richardjm/Crucible/STLs/panels/clip_3.8/panel_clip_corner_3.8.stl

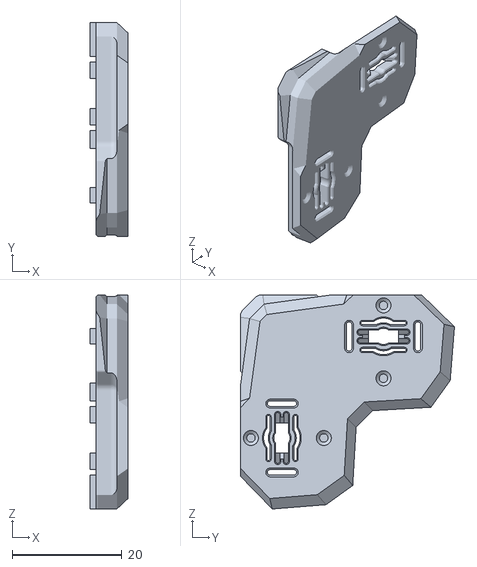
[picture p19: CAD file, 2023-03-05]
STLs/panels/clip_3.8/panel_clip_corner_3.8.stl
6.94 x 38.9 x 38.9
