richardjm/Crucible/STLs/panels/clip_4.8/[t]_panel_key_4.8.stl

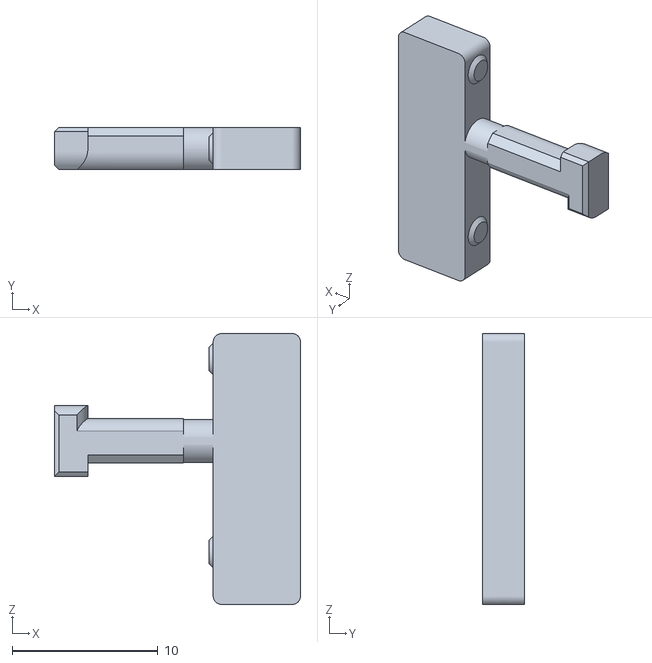
[picture p20: CAD file, 2023-03-05]
STLs/panels/clip_4.8/[t]_panel_key_4.8.stl
16.9 x 2.90 x 18.6
