richardjm/Crucible/STLs/panels/clip_7.0/panel_clip_center_7.0.stl

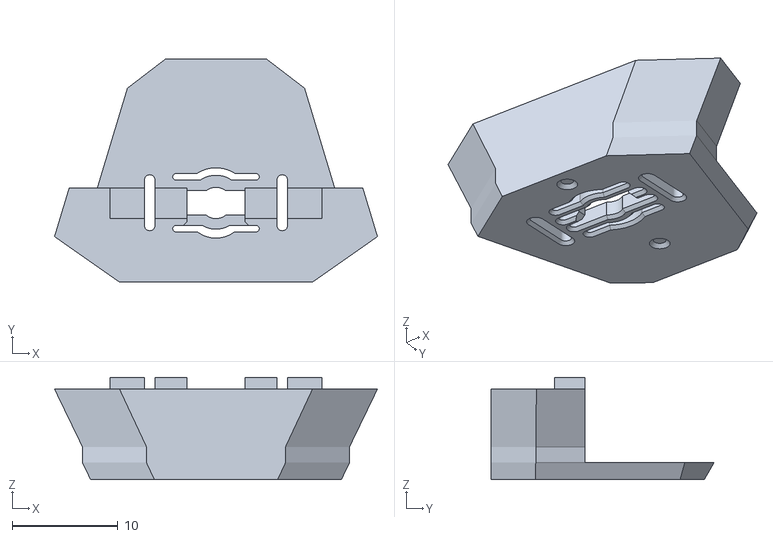
[picture p21: CAD file, 2023-02-03]
STLs/panels/clip_7.0/panel_clip_center_7.0.stl
30.5 x 21.1 x 9.66
