richardjm/Crucible/STLs/spool_holder/[a]_filament_guide_6mm.stl

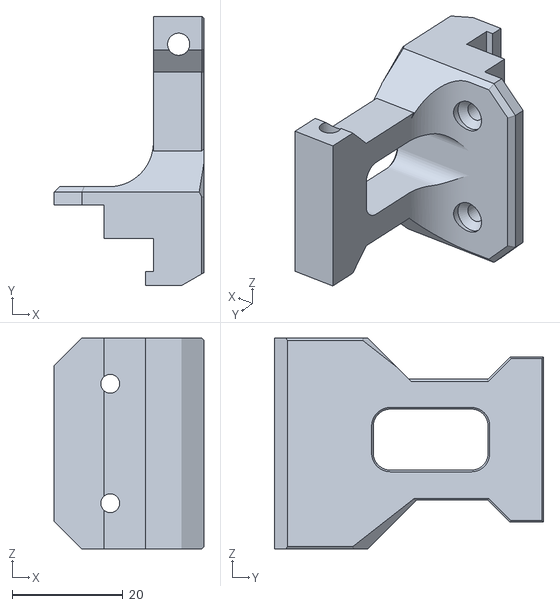
[picture p22: CAD file, 2023-04-07]
STLs/spool_holder/[a]_filament_guide_6mm.stl
27.0 x 48.5 x 38.0
