richardjm/Crucible/STLs/spoolholder.stl

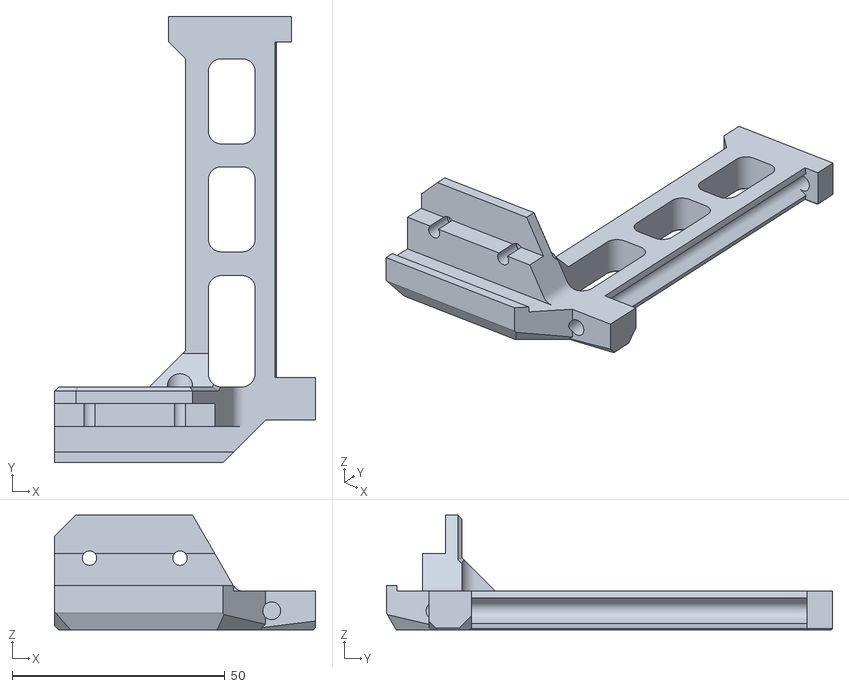
[picture p23: CAD file, 2023-01-31]
STLs/spoolholder.stl
61.4 x 105.0 x 27.0
