richardjm/Crucible/STLs/stealth_skirts/4010_Side_Skirt_Mid_Solid_x2.stl

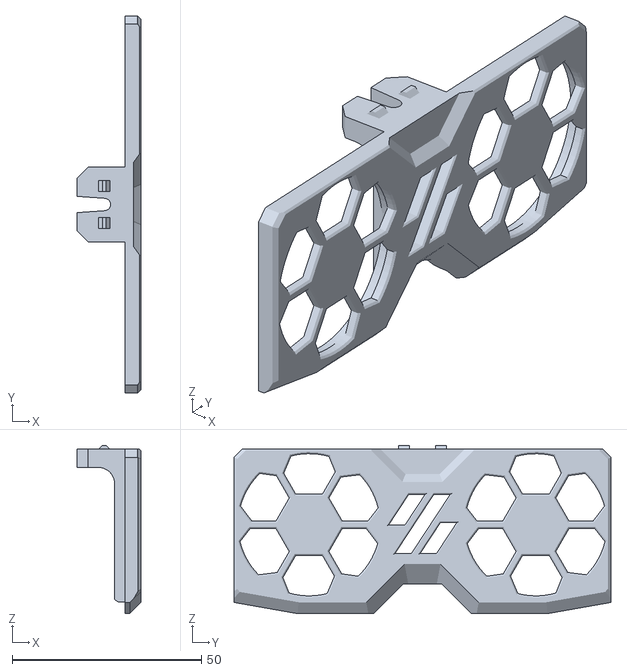
[picture p24: CAD file, 2023-04-01]
STLs/stealth_skirts/4010_Side_Skirt_Mid_Solid_x2.stl
17.0 x 99.7 x 44.5
