richardjm/Crucible/STLs/tools/MGN9_Rail_Guide_x2.stl

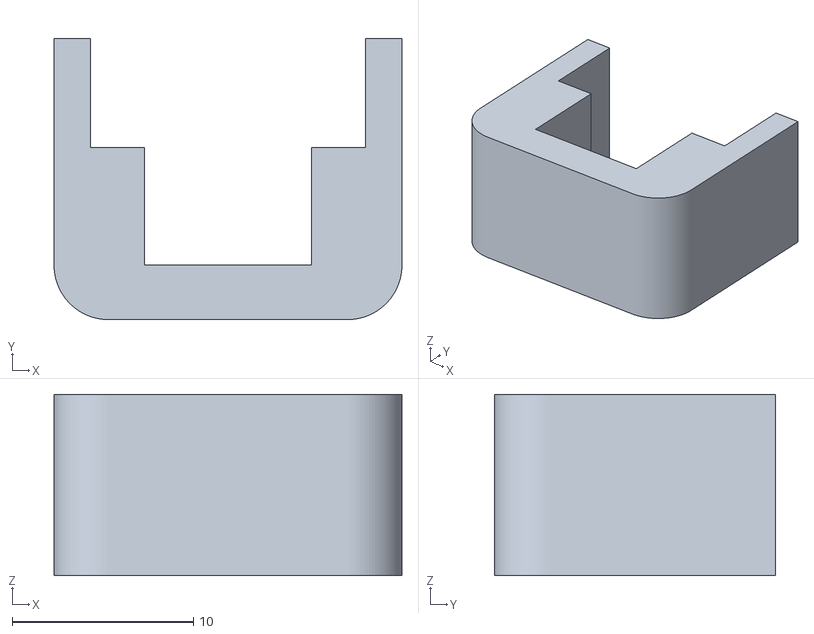
[picture p25: CAD file, 2023-02-28]
STLs/tools/MGN9_Rail_Guide_x2.stl
19.2 x 15.5 x 10.0
