richardjm/Crucible/Usermods/richardjm/carriage-slimmed/[a]_x_carriage-5.95.stl

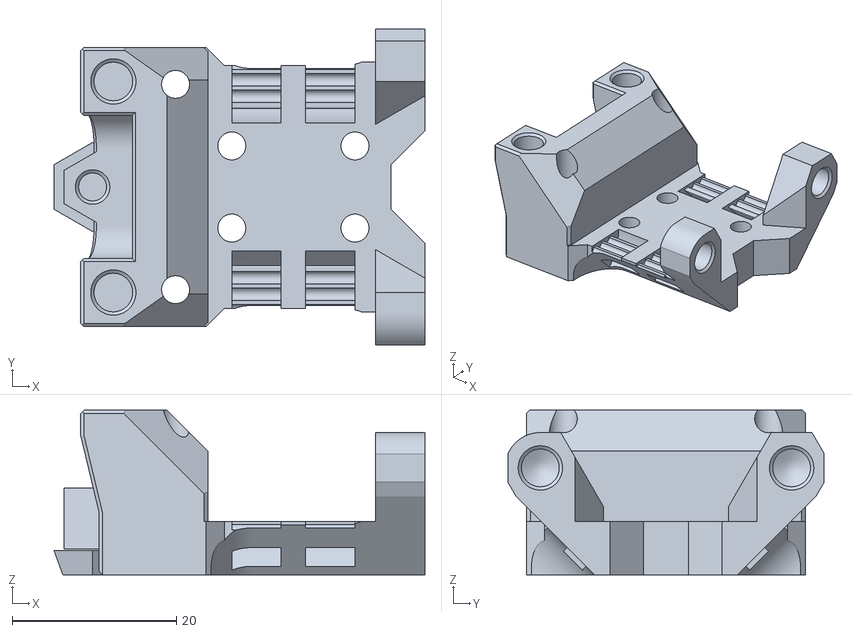
[picture p26: CAD file, 2023-02-17]
Usermods/richardjm/carriage-slimmed/[a]_x_carriage-5.95.stl
45.2 x 38.5 x 20.1
