richardjm/Crucible/Usermods/richardjm/extrusionless-x/boop/magnet_carrier_right.stl

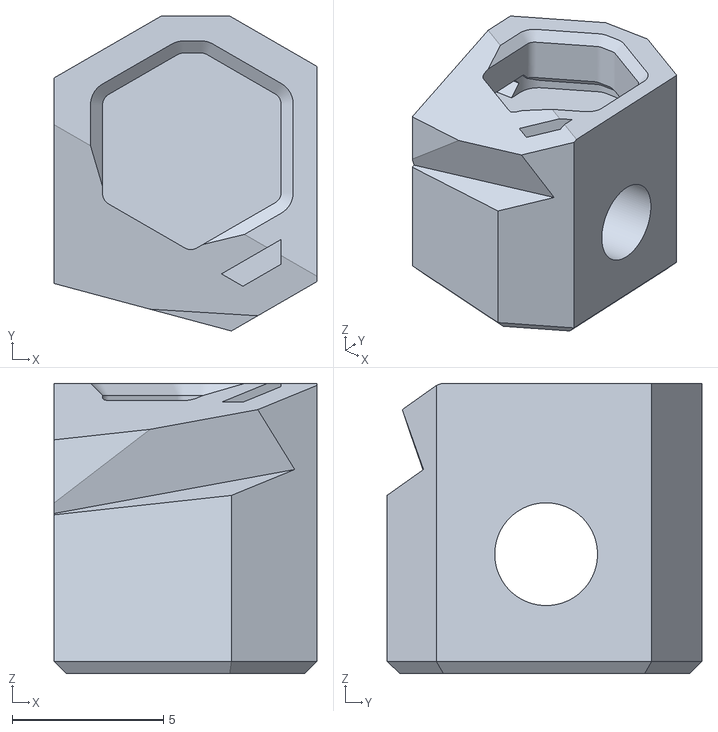
[picture p28: CAD file, 2025-10-05]
Usermods/richardjm/extrusionless-x/boop/magnet_carrier_right.stl
8.70 x 10.4 x 9.60
