richardjm/Crucible/Usermods/richardjm/flysht36-mount/FlySht36v2Mount.stl

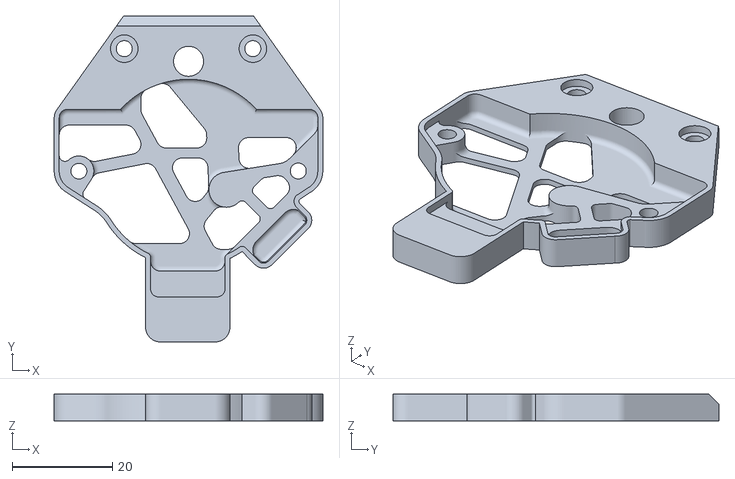
[picture p30: CAD file, 2023-02-16]
Usermods/richardjm/flysht36-mount/FlySht36v2Mount.stl
53.7 x 65.1 x 5.33
