richardjm/Crucible/Usermods/richardjm/frond-bed-cover/FrontBedCover-15mmBrassSpacer.stl

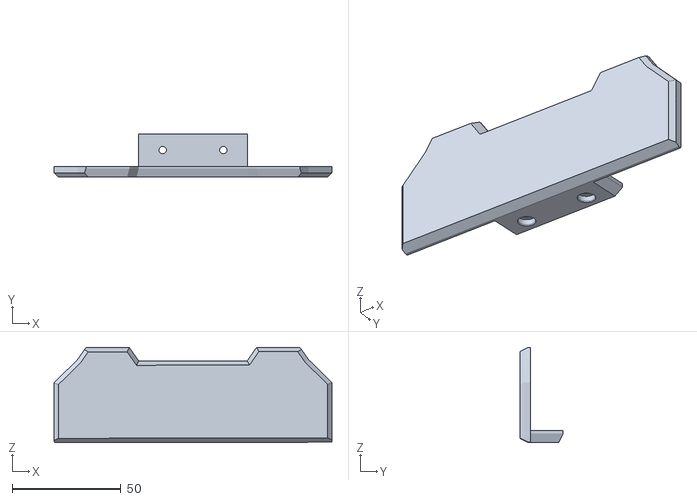
[picture p31: CAD file, 2023-03-17]
Usermods/richardjm/frond-bed-cover/FrontBedCover-15mmBrassSpacer.stl
128.1 x 20.0 x 43.9
