richardjm/Crucible/Usermods/richardjm/idle_idea/IdleIdea2 v13 - CarrierA.stl

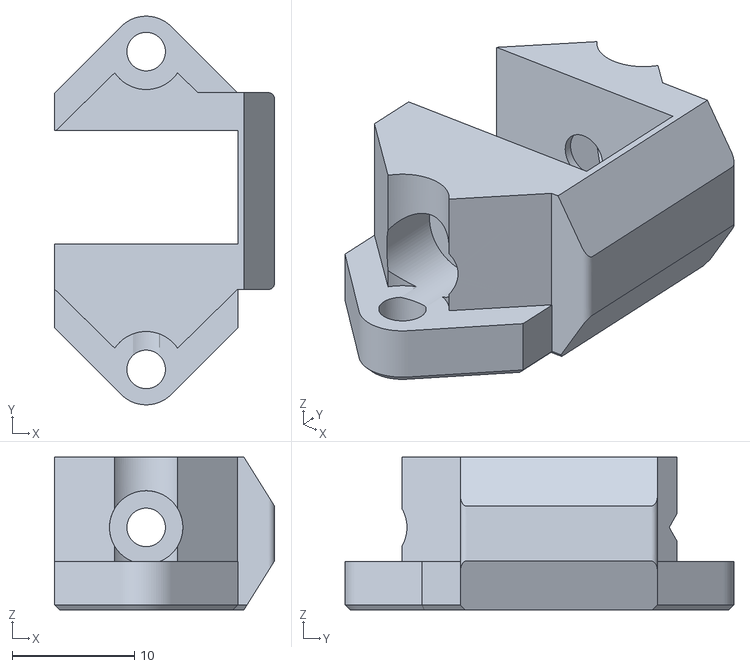
[picture p32: CAD file, 2023-04-13]
Usermods/richardjm/idle_idea/IdleIdea2 v13 - CarrierA.stl
18.0 x 31.8 x 12.5
