richardjm/Crucible/Usermods/richardjm/idler_beefy/idler_b_arm.stl

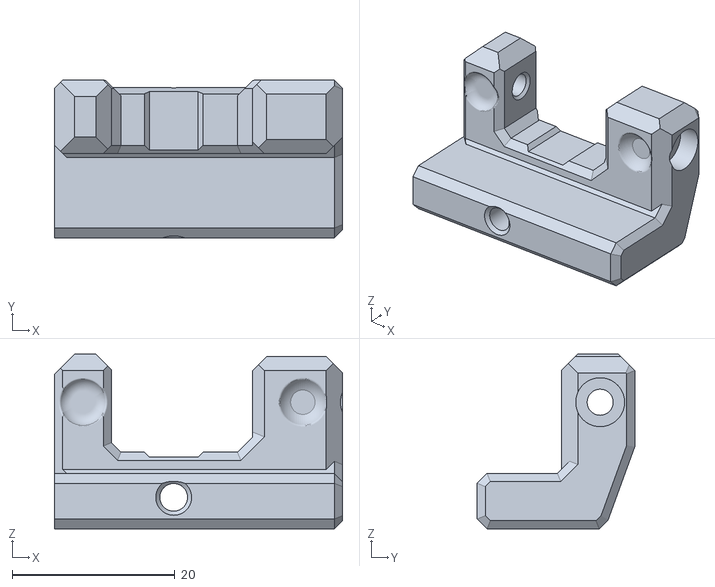
[picture p33: CAD file, 2023-04-13]
Usermods/richardjm/idler_beefy/idler_b_arm.stl
35.4 x 19.4 x 21.4
