richardjm/Crucible/Usermods/richardjm/leds/crucible_led_sawtooth_100mm.stl

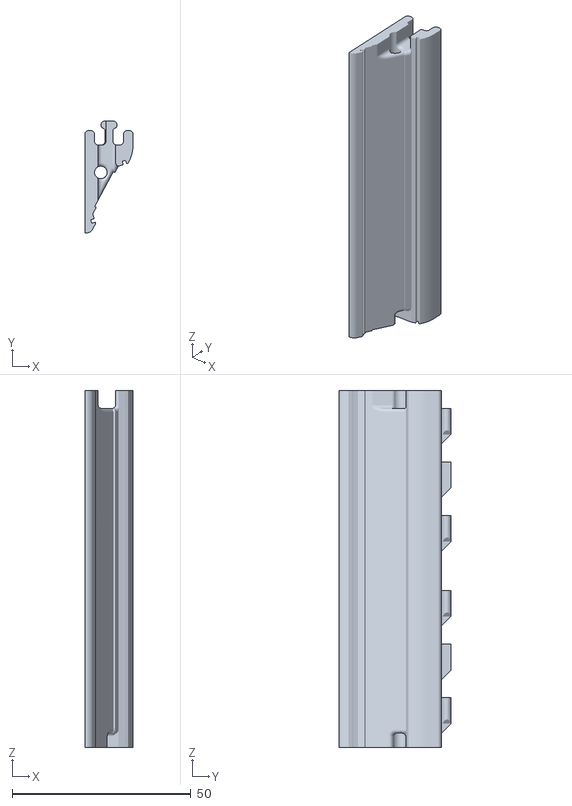
[picture p34: CAD file, 2023-02-11]
Usermods/richardjm/leds/crucible_led_sawtooth_100mm.stl
13.5 x 31.4 x 100.0
