richardjm/Crucible/Usermods/richardjm/pointy-stop/rail-stop.stl

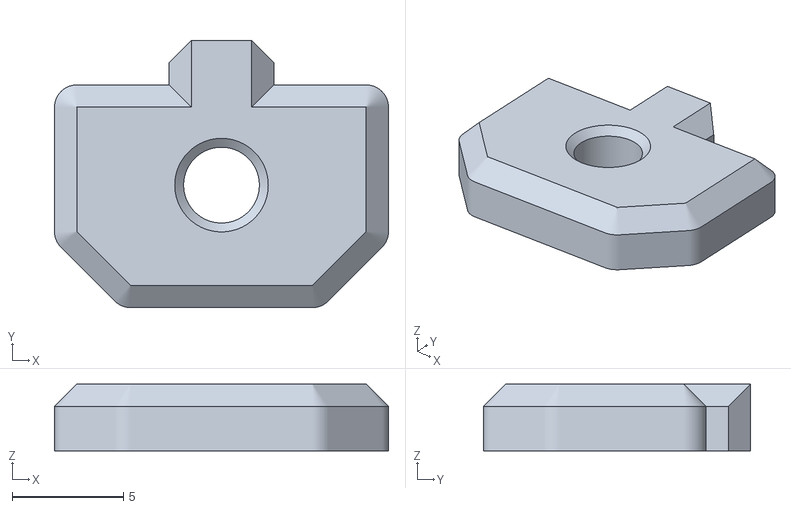
[picture p35: CAD file, 2023-02-24]
Usermods/richardjm/pointy-stop/rail-stop.stl
15.0 x 12.0 x 3.00
