richardjm/Crucible/Usermods/richardjm/puppet-pi-mount/PuppetPi.stl

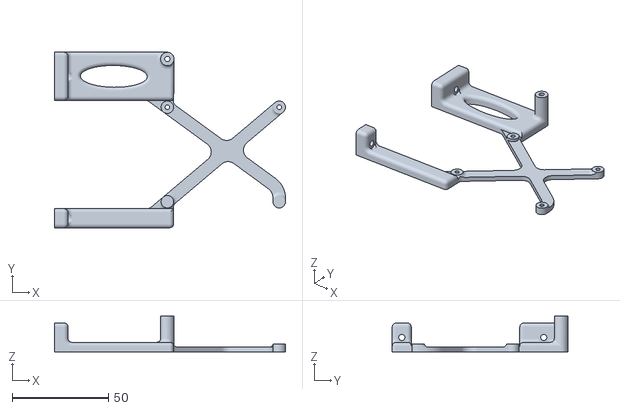
[picture p36: CAD file, 2023-03-19]
Usermods/richardjm/puppet-pi-mount/PuppetPi.stl
119.8 x 91.0 x 18.6
