richardjm/Crucible/Usermods/richardjm/short-rear-z/Z_ChainMount_w_cable.stl

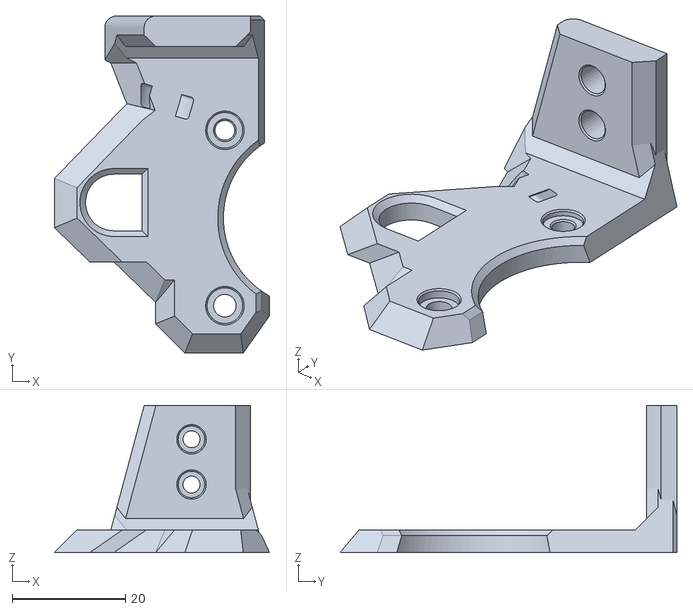
[picture p37: CAD file, 2023-03-19]
Usermods/richardjm/short-rear-z/Z_ChainMount_w_cable.stl
38.0 x 59.6 x 26.0
