richardjm/Crucible/Usermods/richardjm/UnKlickyNG/STL/ProbeMount_Body3_Wedge.stl

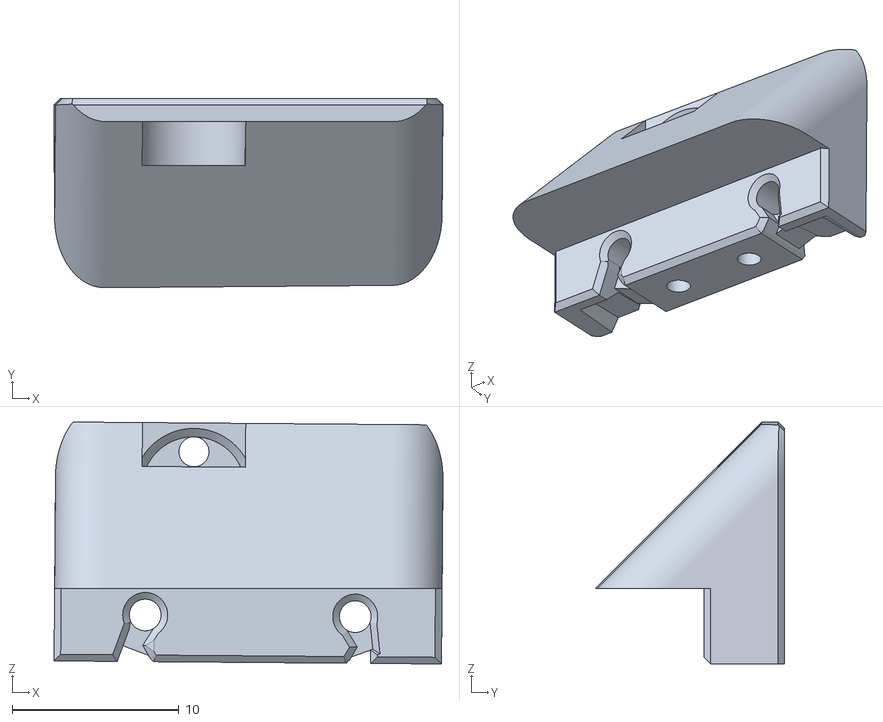
[picture p38: CAD file, 2023-03-13]
Usermods/richardjm/UnKlickyNG/STL/ProbeMount_Body3_Wedge.stl
23.3 x 11.4 x 14.5
