richardjm/Crucible/STLs/frame/[a]_rail_stop_x6.stl

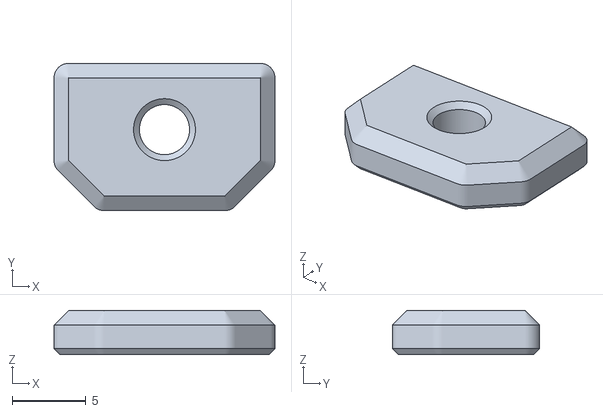
[picture p39: CAD file, 2023-02-13]
STLs/frame/[a]_rail_stop_x6.stl
15.0 x 10.0 x 3.00
