richardjm/Crucible/STLs/gantry/a_drive_lower_no_fittings.stl

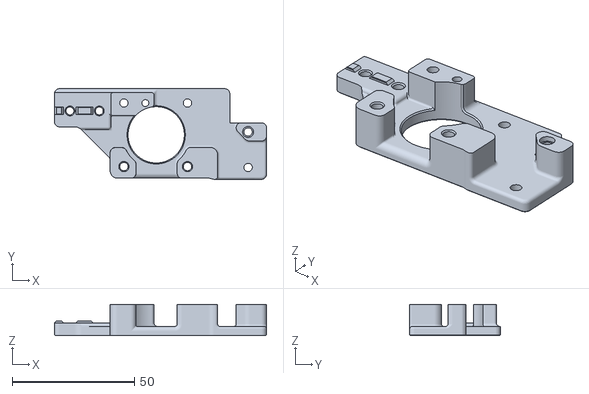
[picture p40: CAD file, 2023-02-12]
STLs/gantry/a_drive_lower_no_fittings.stl
86.7 x 37.0 x 12.8
