richardjm/Crucible/STLs/handles/[t]_handle_part2_x2.stl.stl

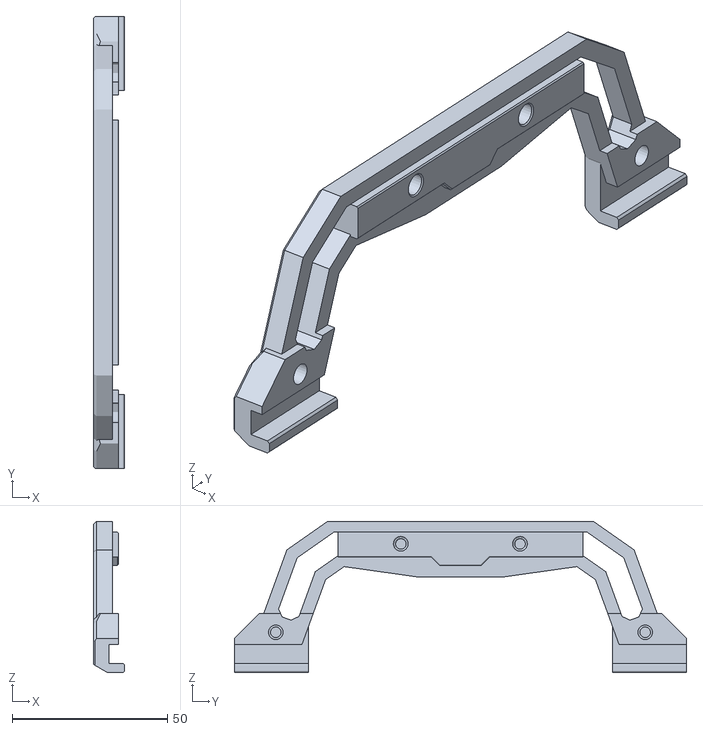
[picture p41: CAD file, 2023-04-07]
STLs/handles/[t]_handle_part2_x2.stl.stl
10.0 x 145.7 x 48.8
