richardjm/Crucible/STLs/klicky/probe.stl

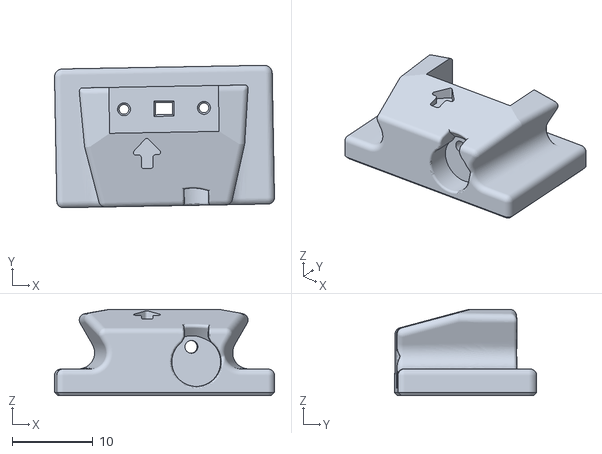
[picture p42: CAD file, 2023-02-26]
STLs/klicky/probe.stl
27.3 x 17.7 x 10.7
