richardjm/Crucible/STLs/mini_stealthburner/[a]_front_cowling.stl

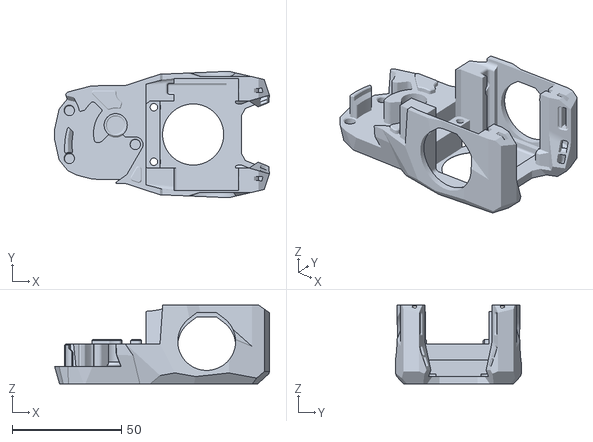
[picture p43: CAD file, 2023-02-13]
STLs/mini_stealthburner/[a]_front_cowling.stl
98.6 x 57.9 x 36.1
