richardjm/Crucible/STLs/mini_stealthburner/hotends/[a]_Hotend_Mount_Revo_Voron.stl

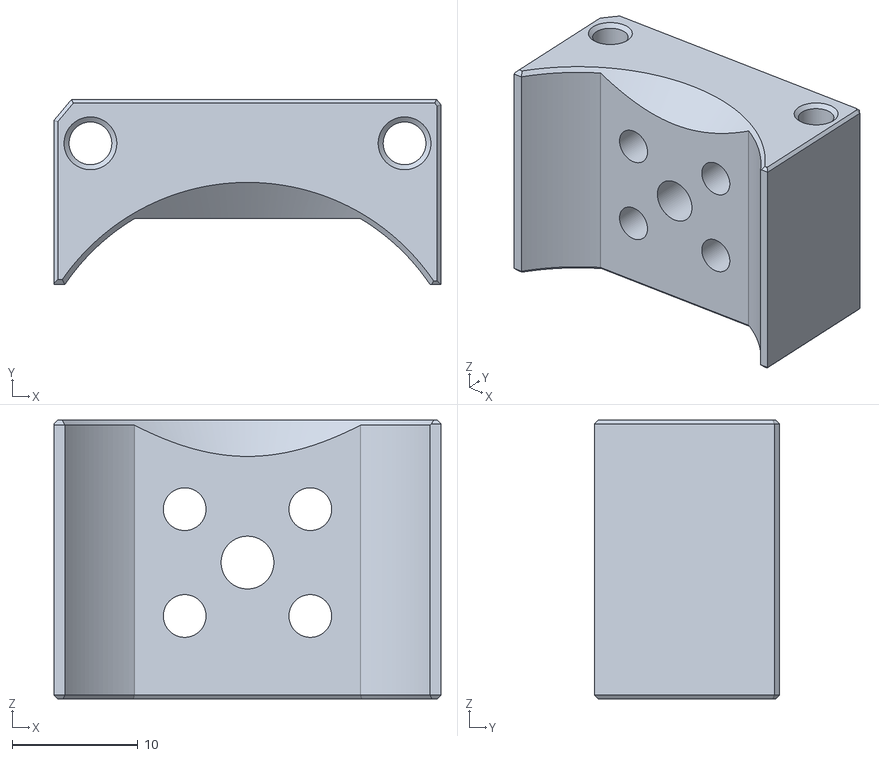
[picture p44: CAD file, 2023-02-12]
STLs/mini_stealthburner/hotends/[a]_Hotend_Mount_Revo_Voron.stl
30.8 x 14.7 x 22.2
