richardjm/Crucible/STLs/panels/clip_2.8/panel_clip_center_2.8.stl

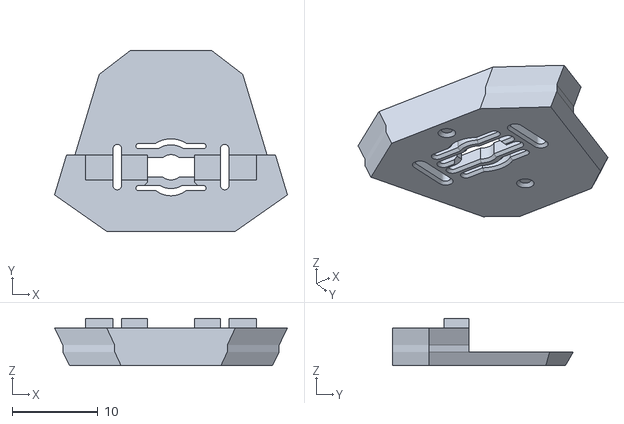
[picture p45: CAD file, 2023-02-04]
STLs/panels/clip_2.8/panel_clip_center_2.8.stl
27.2 x 21.1 x 5.50
