richardjm/Crucible/STLs/panels/clip_3.8/panel_clip_center_3.8.stl

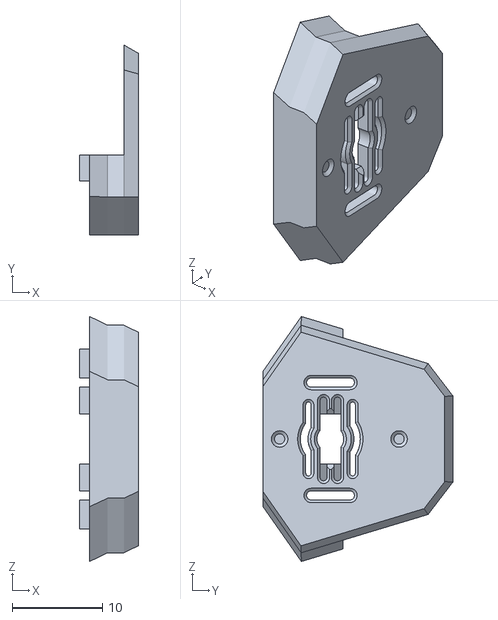
[picture p46: CAD file, 2023-03-05]
STLs/panels/clip_3.8/panel_clip_center_3.8.stl
6.50 x 21.1 x 27.2
