richardjm/Crucible/STLs/panels/clip_4.8/panel_clip_corner_4.8.stl

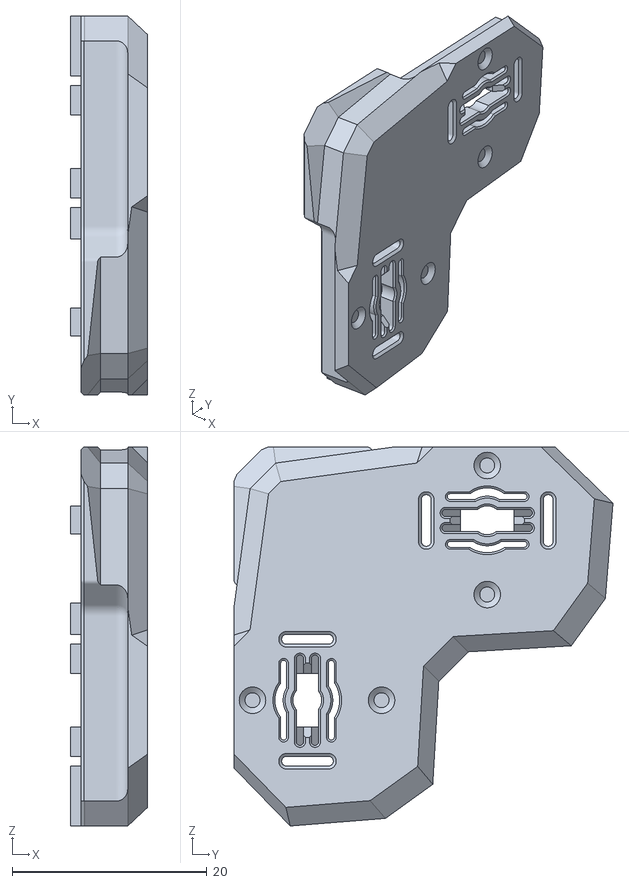
[picture p47: CAD file, 2023-03-05]
STLs/panels/clip_4.8/panel_clip_corner_4.8.stl
7.94 x 38.9 x 38.9
