richardjm/Crucible/STLs/panels/clip_7.0/panel_clip_corner_7.0.stl

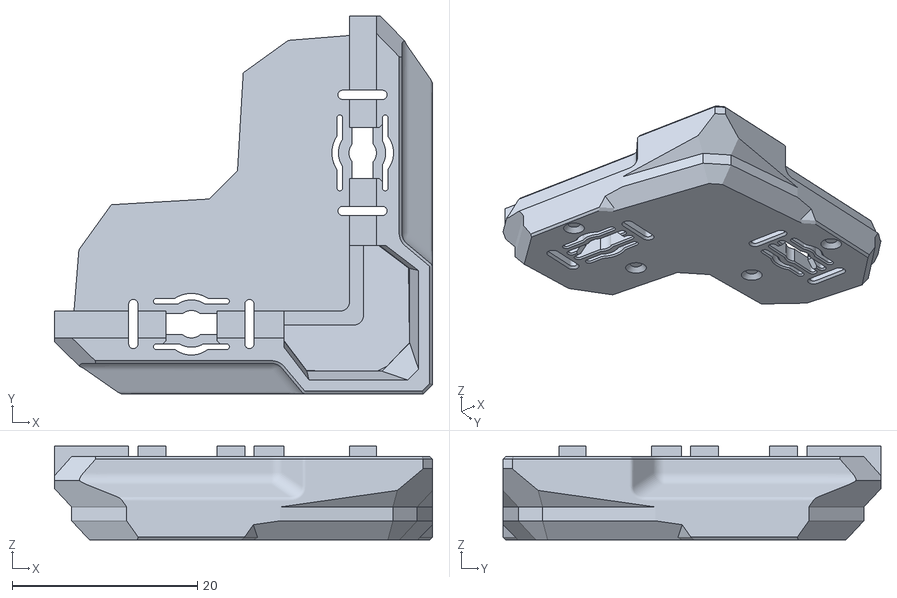
[picture p48: CAD file, 2023-02-03]
STLs/panels/clip_7.0/panel_clip_corner_7.0.stl
40.8 x 40.8 x 10.1
