richardjm/Crucible/STLs/panels/door_hinge_m3x40_x2.stl

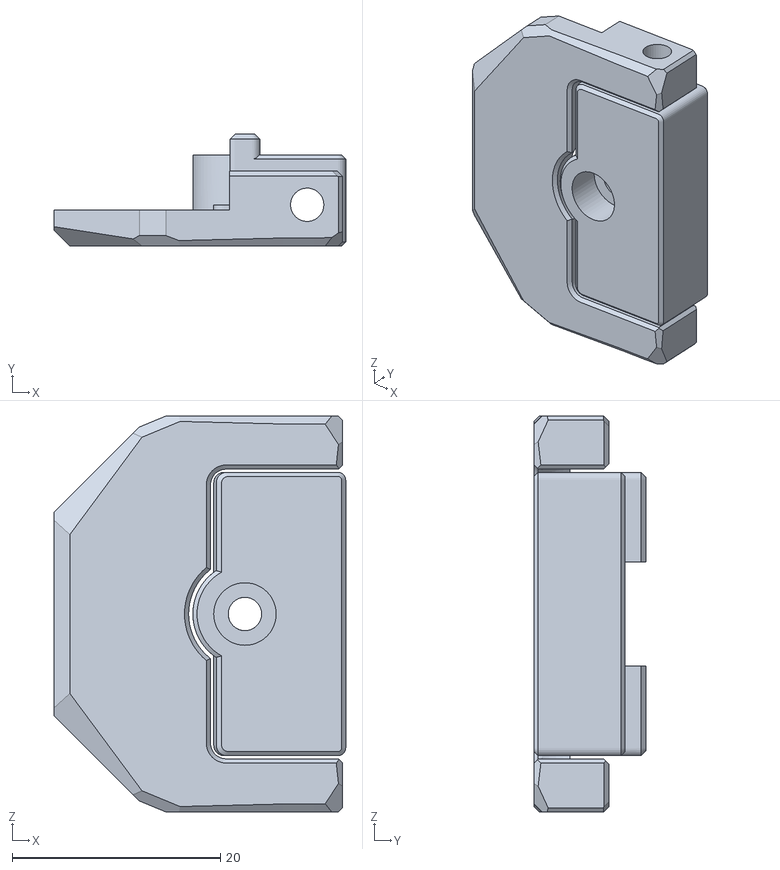
[picture p49: CAD file, 2023-04-02]
STLs/panels/door_hinge_m3x40_x2.stl
28.0 x 10.8 x 38.0
