richardjm/Crucible/STLs/spool_holder/[a]_spool_holder_6mm.stl

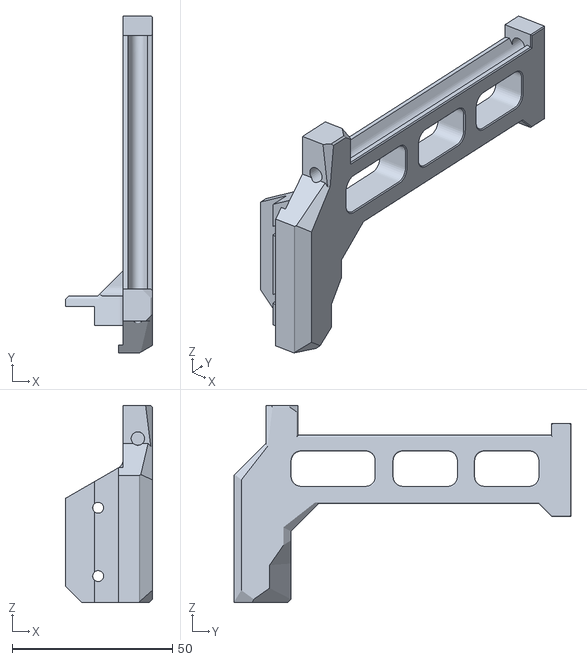
[picture p50: CAD file, 2023-04-07]
STLs/spool_holder/[a]_spool_holder_6mm.stl
27.0 x 105.0 x 61.4
