richardjm/Crucible/STLs/stealth_skirts/Rear_Skirt_Crucible_x1.stl

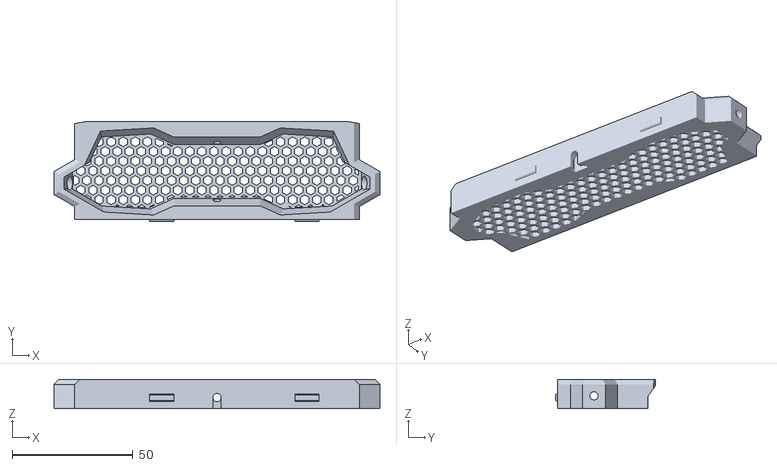
[picture p51: CAD file, 2023-04-01]
STLs/stealth_skirts/Rear_Skirt_Crucible_x1.stl
134.7 x 41.5 x 12.0
