richardjm/Crucible/STLs/z_assembly/z_rear_lower_circular_tnut.stl

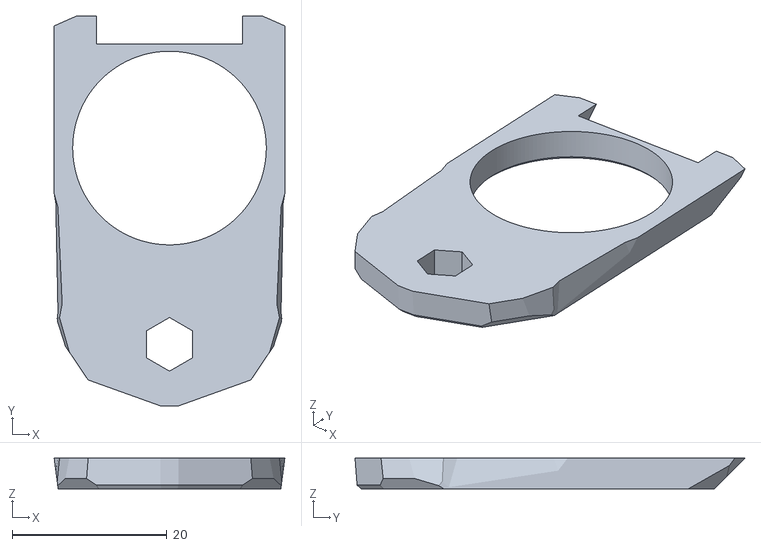
[picture p52: CAD file, 2023-02-11]
STLs/z_assembly/z_rear_lower_circular_tnut.stl
29.8 x 50.4 x 4.00
