richardjm/Crucible/Usermods/richardjm/carriage-slimmed/[a]_strain_relief_spacer_extra_beef-5.95_x2.stl

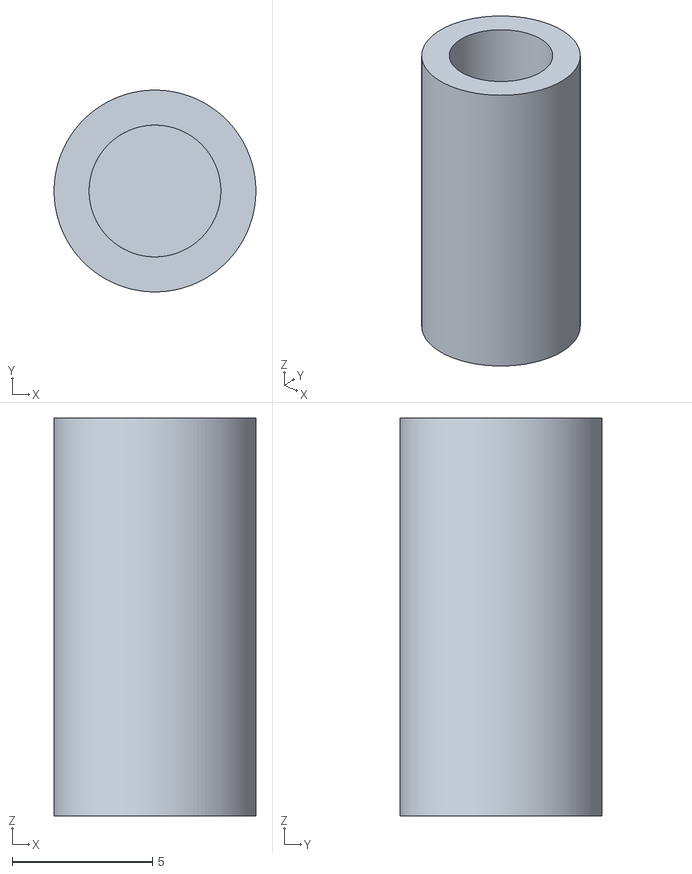
[picture p53: CAD file, 2023-02-17]
Usermods/richardjm/carriage-slimmed/[a]_strain_relief_spacer_extra_beef-5.95_x2.stl
7.20 x 7.20 x 14.2
