richardjm/Crucible/Usermods/richardjm/everywhere-brace/[a]z_right_lower_sliced.stl

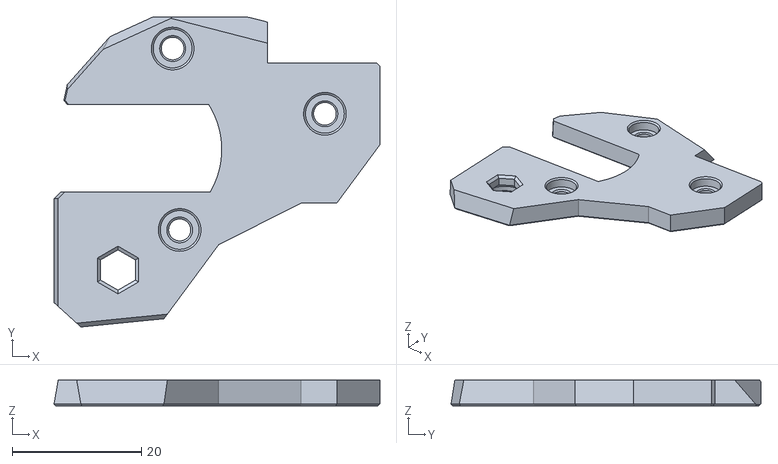
[picture p54: CAD file, 2023-11-12]
Usermods/richardjm/everywhere-brace/[a]z_right_lower_sliced.stl
50.4 x 48.0 x 4.00
