richardjm/Crucible/Usermods/richardjm/extrusionless-x/boop/magnet_carrier_left.stl

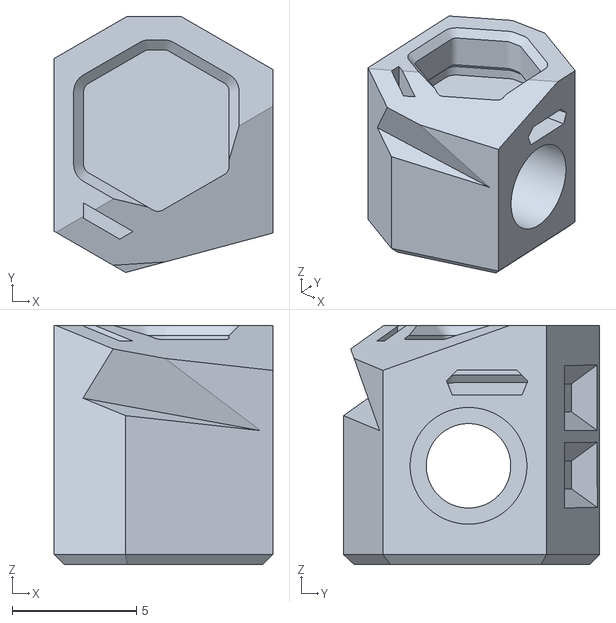
[picture p55: CAD file, 2025-10-05]
Usermods/richardjm/extrusionless-x/boop/magnet_carrier_left.stl
8.80 x 10.3 x 9.63
