richardjm/Crucible/Usermods/richardjm/extrusionless-x/XY_Joint_Left_RailSupport.stl

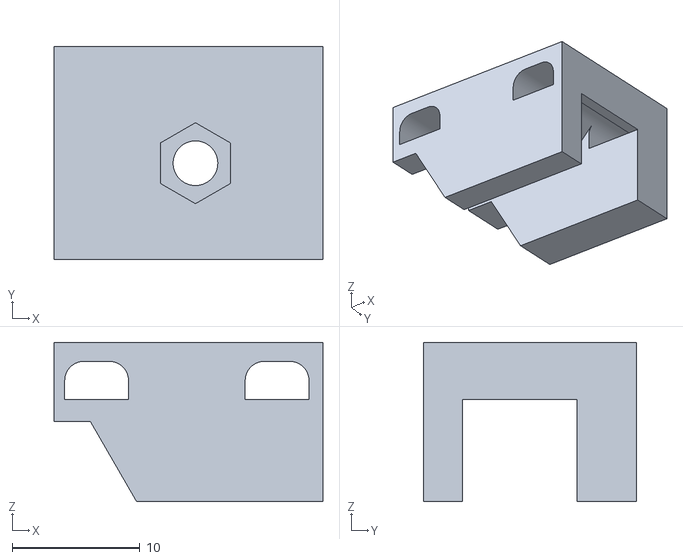
[picture p56: CAD file, 2025-10-05]
Usermods/richardjm/extrusionless-x/XY_Joint_Left_RailSupport.stl
21.1 x 16.7 x 12.5
