richardjm/Crucible/Usermods/richardjm/frond-bed-cover/FrontBedCover.stl

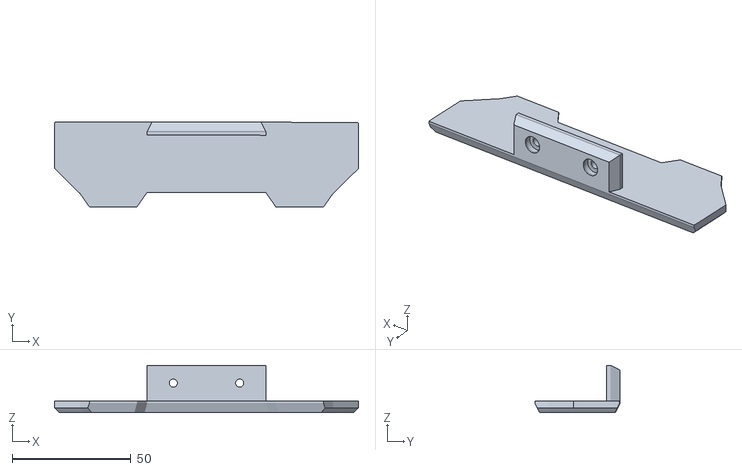
[picture p57: CAD file, 2023-03-04]
Usermods/richardjm/frond-bed-cover/FrontBedCover.stl
128.1 x 35.9 x 20.0
