richardjm/Crucible/Usermods/richardjm/idler_beefy/idler_b_plate.stl

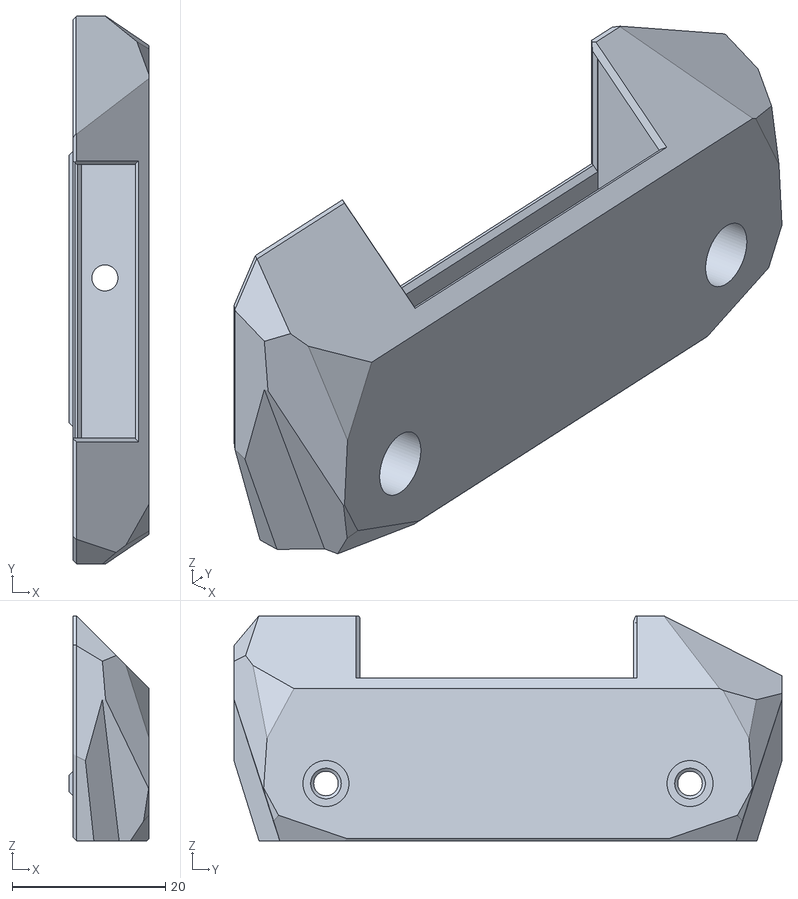
[picture p58: CAD file, 2023-03-04]
Usermods/richardjm/idler_beefy/idler_b_plate.stl
10.5 x 71.5 x 29.3
