richardjm/Crucible/Usermods/richardjm/leds/crucible_led_sawtooth_199mm.stl

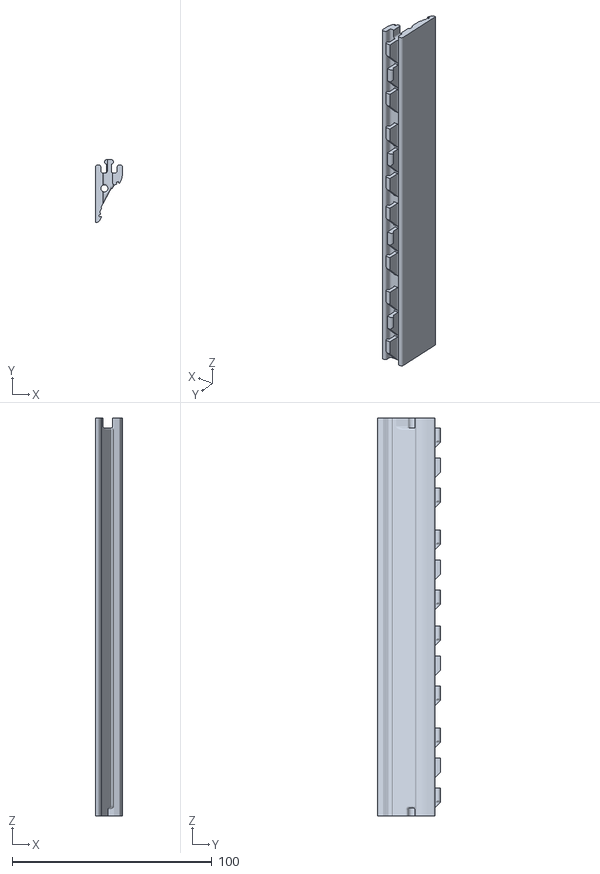
[picture p59: CAD file, 2023-02-11]
Usermods/richardjm/leds/crucible_led_sawtooth_199mm.stl
13.5 x 31.4 x 199.0
