richardjm/Crucible/Usermods/richardjm/puppet-pi-mount/Spacer1_x2.stl

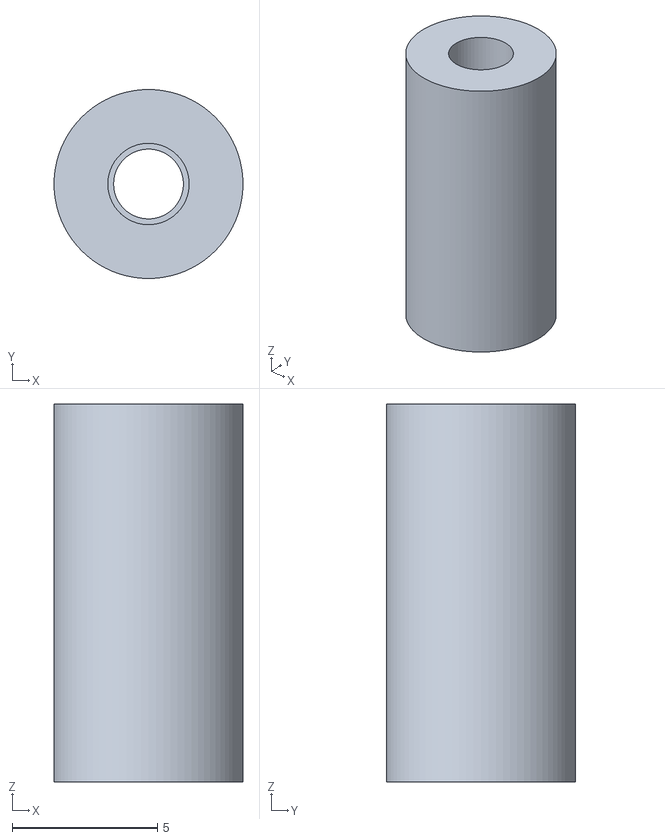
[picture p60: CAD file, 2023-03-19]
Usermods/richardjm/puppet-pi-mount/Spacer1_x2.stl
6.50 x 6.50 x 13.0
