richardjm/Crucible/Usermods/richardjm/short-rear-z/z_stepper_rear_w_cable.stl

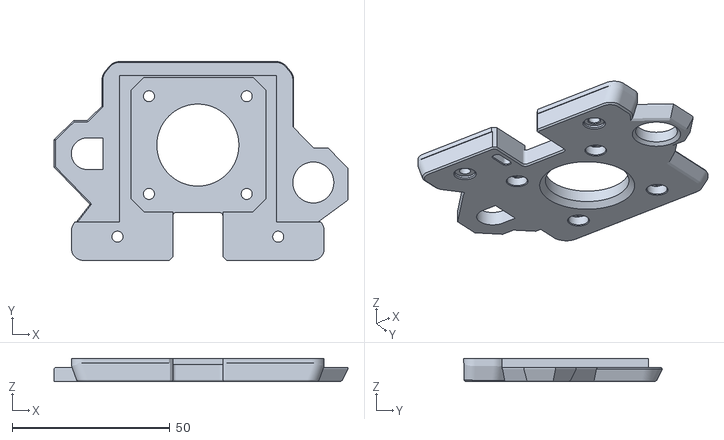
[picture p61: CAD file, 2023-03-17]
Usermods/richardjm/short-rear-z/z_stepper_rear_w_cable.stl
93.2 x 63.1 x 7.45
