richardjm/Crucible/Usermods/richardjm/UnKlickyNG/STL/KlickyNG_BFP_Unklicky_WhistlinRic_Back.stl

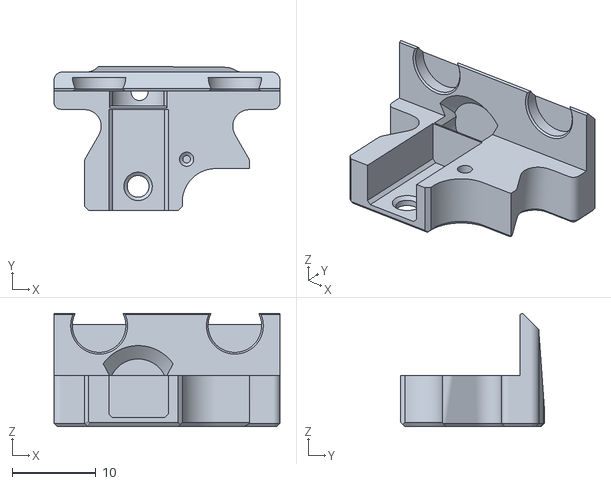
[picture p62: CAD file, 2023-03-06]
Usermods/richardjm/UnKlickyNG/STL/KlickyNG_BFP_Unklicky_WhistlinRic_Back.stl
27.0 x 17.2 x 13.5
