richardjm/Crucible/STLs/display/[c]_Display_Diffuser.STL

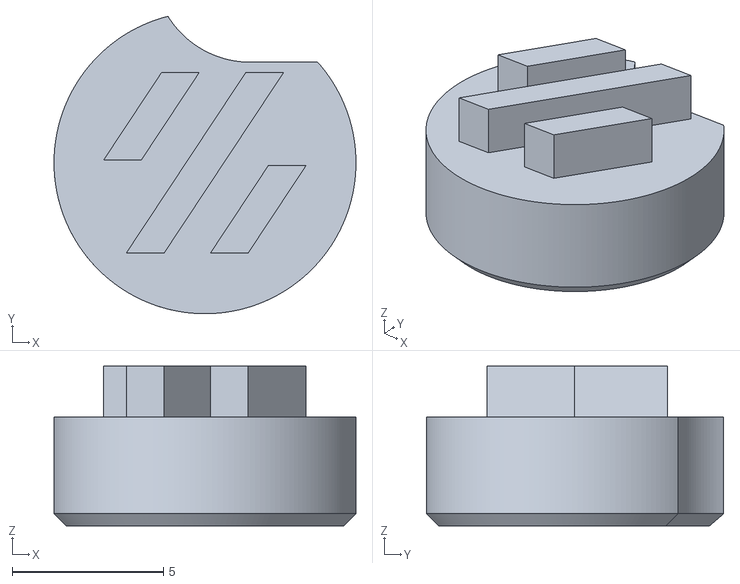
[picture p63: CAD file, 2023-03-23]
STLs/display/[c]_Display_Diffuser.STL
10.00 x 9.85 x 5.28
