richardjm/Crucible/STLs/frame/rear_vertical_brace_m3x20.stl

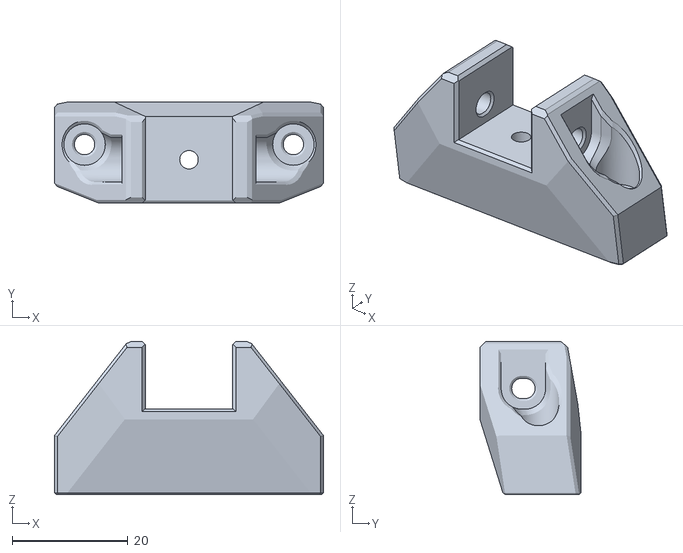
[picture p64: CAD file, 2023-02-11]
STLs/frame/rear_vertical_brace_m3x20.stl
46.5 x 17.5 x 26.4
