richardjm/Crucible/STLs/gantry/b_drive_lower.stl

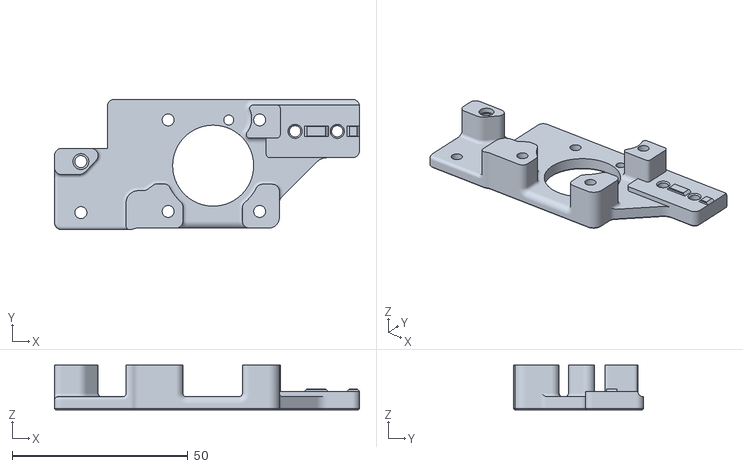
[picture p65: CAD file, 2023-02-12]
STLs/gantry/b_drive_lower.stl
86.7 x 37.0 x 12.8
