richardjm/Crucible/STLs/mini_stealthburner/[t]_guidler.stl

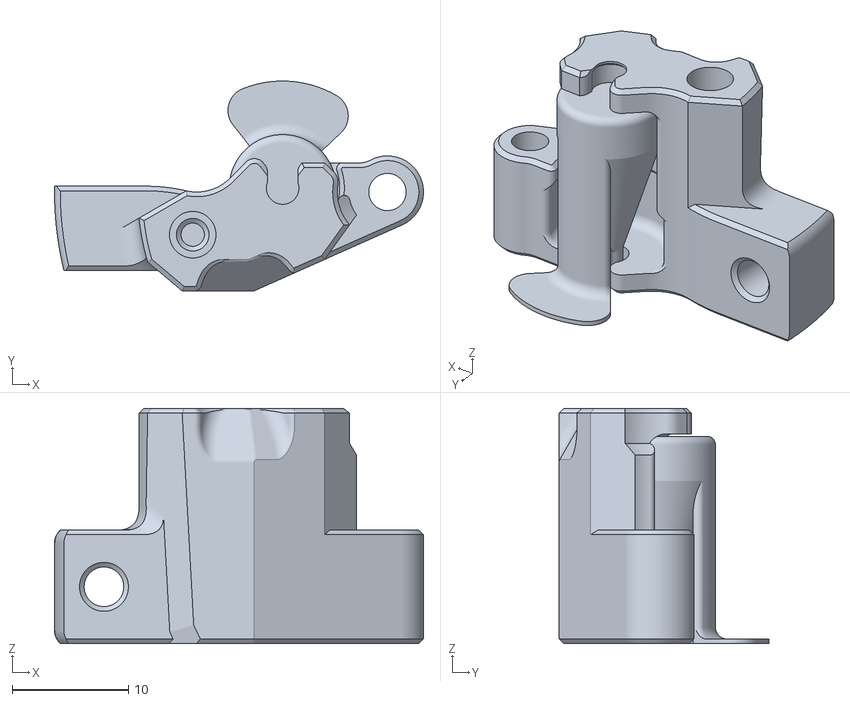
[picture p66: CAD file, 2023-02-12]
STLs/mini_stealthburner/[t]_guidler.stl
31.7 x 18.0 x 20.2
