richardjm/Crucible/STLs/mini_stealthburner/hotends/[a]_FS_Hotend_Mount_Dragon.stl

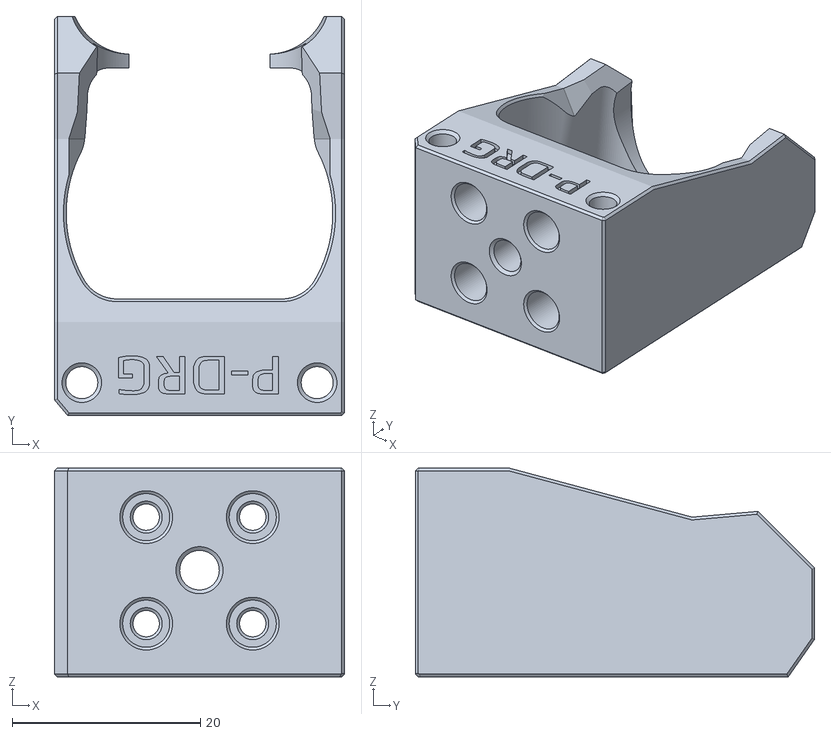
[picture p67: CAD file, 2023-02-12]
STLs/mini_stealthburner/hotends/[a]_FS_Hotend_Mount_Dragon.stl
30.8 x 42.4 x 22.2
