richardjm/Crucible/STLs/panels/clip_2.8/panel_clip_corner_2.8.stl

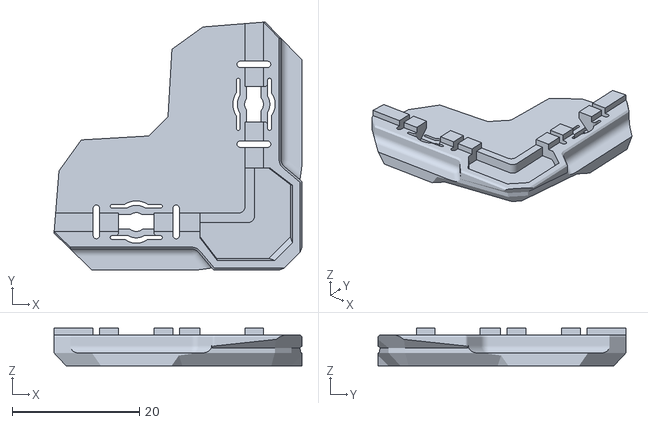
[picture p68: CAD file, 2023-02-04]
STLs/panels/clip_2.8/panel_clip_corner_2.8.stl
38.9 x 38.9 x 5.94
