richardjm/Crucible/STLs/panels/clip_3.8/[t]_panel_key_3.8.stl

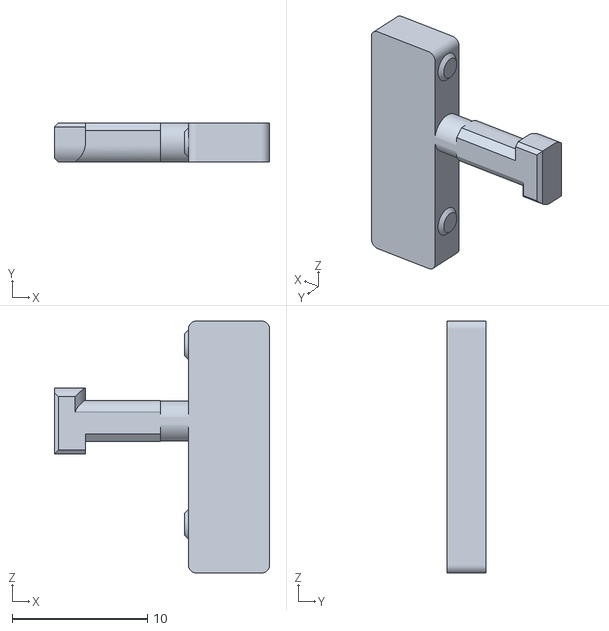
[picture p69: CAD file, 2023-03-05]
STLs/panels/clip_3.8/[t]_panel_key_3.8.stl
15.9 x 2.90 x 18.6
