richardjm/Crucible/STLs/panels/clip_4.8/panel_clip_center_4.8.stl

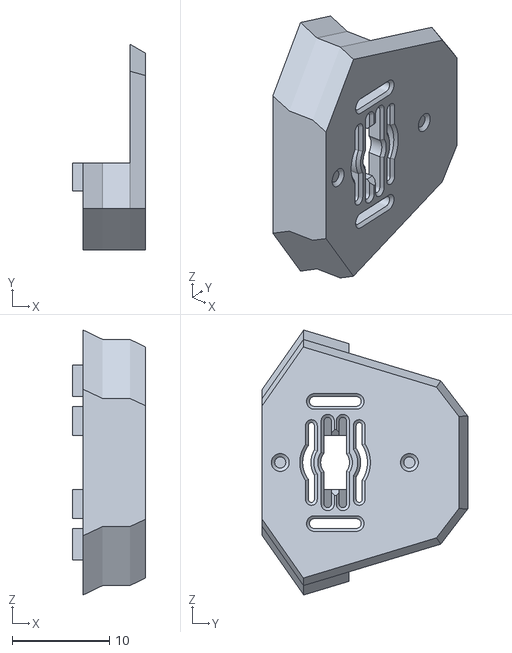
[picture p70: CAD file, 2023-03-05]
STLs/panels/clip_4.8/panel_clip_center_4.8.stl
7.50 x 21.1 x 27.2
