richardjm/Crucible/STLs/panels/clip_7.0/[t]_panel_key_7.0.stl

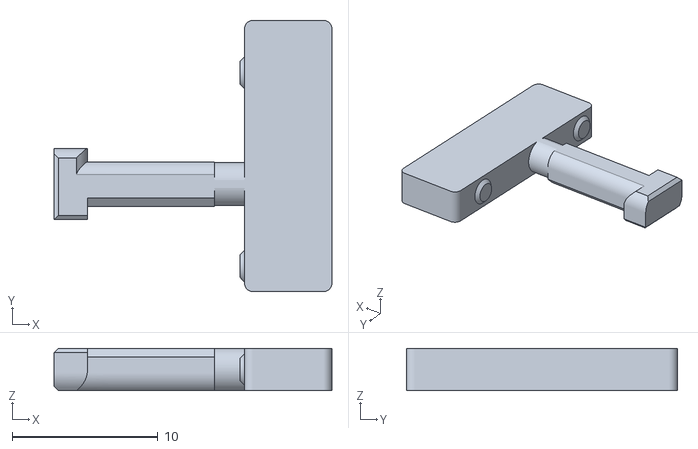
[picture p71: CAD file, 2023-01-31]
STLs/panels/clip_7.0/[t]_panel_key_7.0.stl
19.1 x 18.6 x 2.90
