richardjm/Crucible/STLs/panels/panel_clip_rear.stl

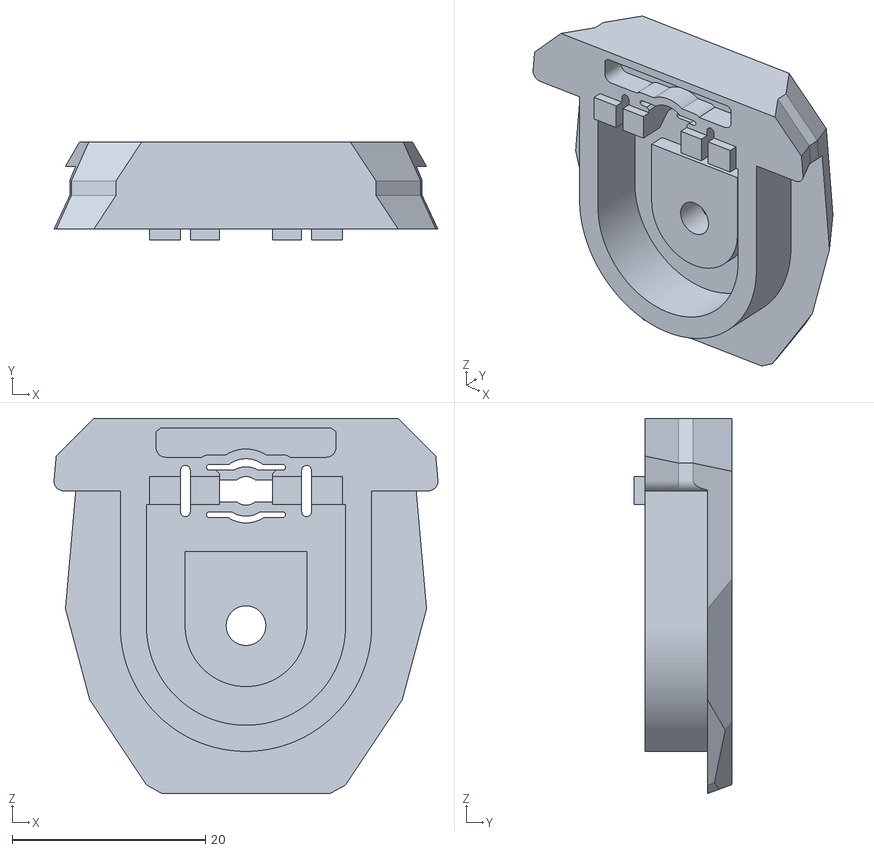
[picture p72: CAD file, 2023-01-31]
STLs/panels/panel_clip_rear.stl
39.7 x 10.1 x 38.8
