richardjm/Crucible/STLs/stealth_skirts/Display_Blankingplate.stl

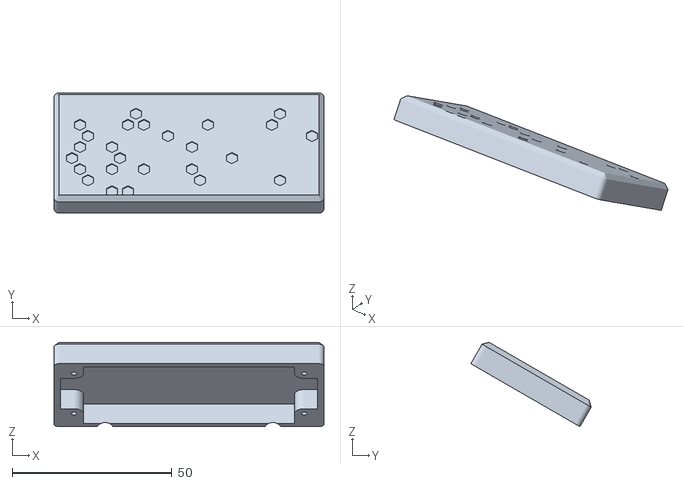
[picture p73: CAD file, 2023-04-01]
STLs/stealth_skirts/Display_Blankingplate.stl
84.4 x 37.6 x 26.4
