richardjm/Crucible/STLs/tools/y_extrusion_positioner.stl

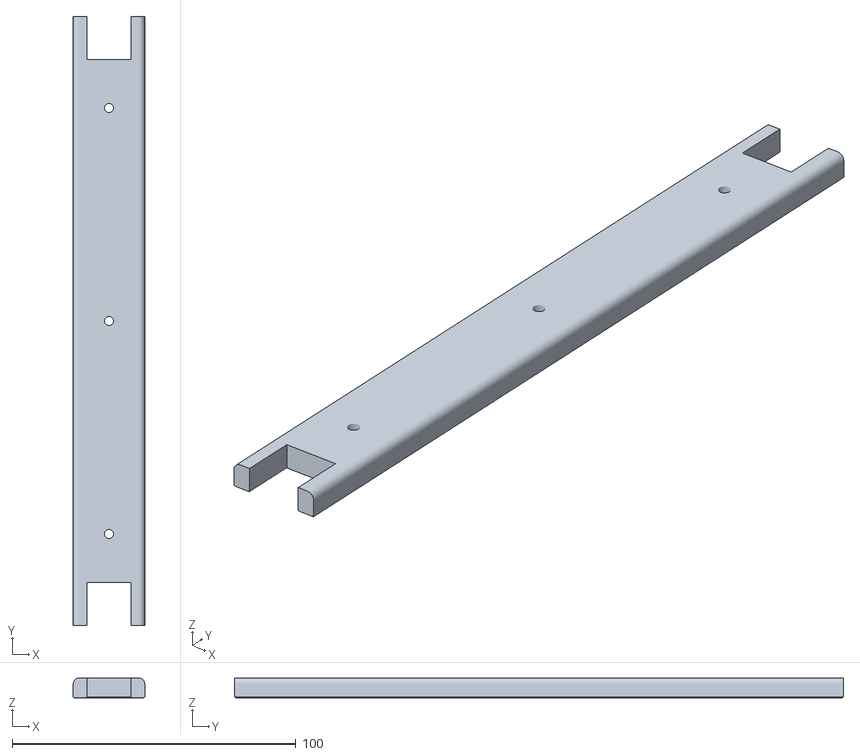
[picture p74: CAD file, 2023-02-13]
STLs/tools/y_extrusion_positioner.stl
25.2 x 214.5 x 7.00
