richardjm/Crucible/Usermods/richardjm/carriage-slimmed/[a]_strain_relief_spacer-4_x2.stl

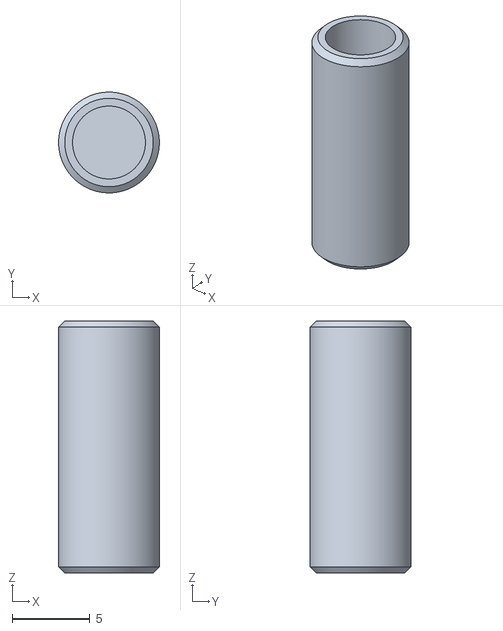
[picture p75: CAD file, 2023-02-16]
Usermods/richardjm/carriage-slimmed/[a]_strain_relief_spacer-4_x2.stl
6.50 x 6.50 x 16.2
