richardjm/Crucible/Usermods/richardjm/extrusionless-x/boop/boop_front.stl

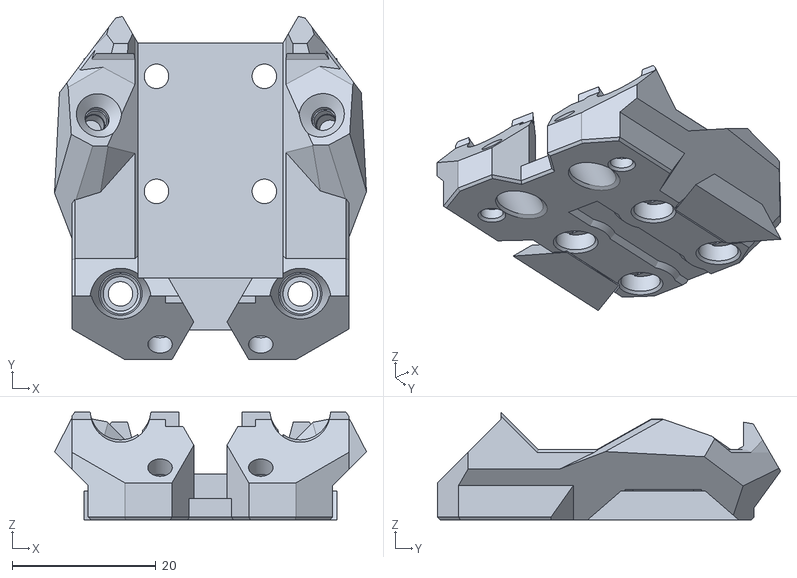
[picture p76: CAD file, 2025-10-05]
Usermods/richardjm/extrusionless-x/boop/boop_front.stl
43.4 x 47.7 x 15.0
