richardjm/Crucible/Usermods/richardjm/idle_idea/IdleIdea2 v13 - BlockA.stl

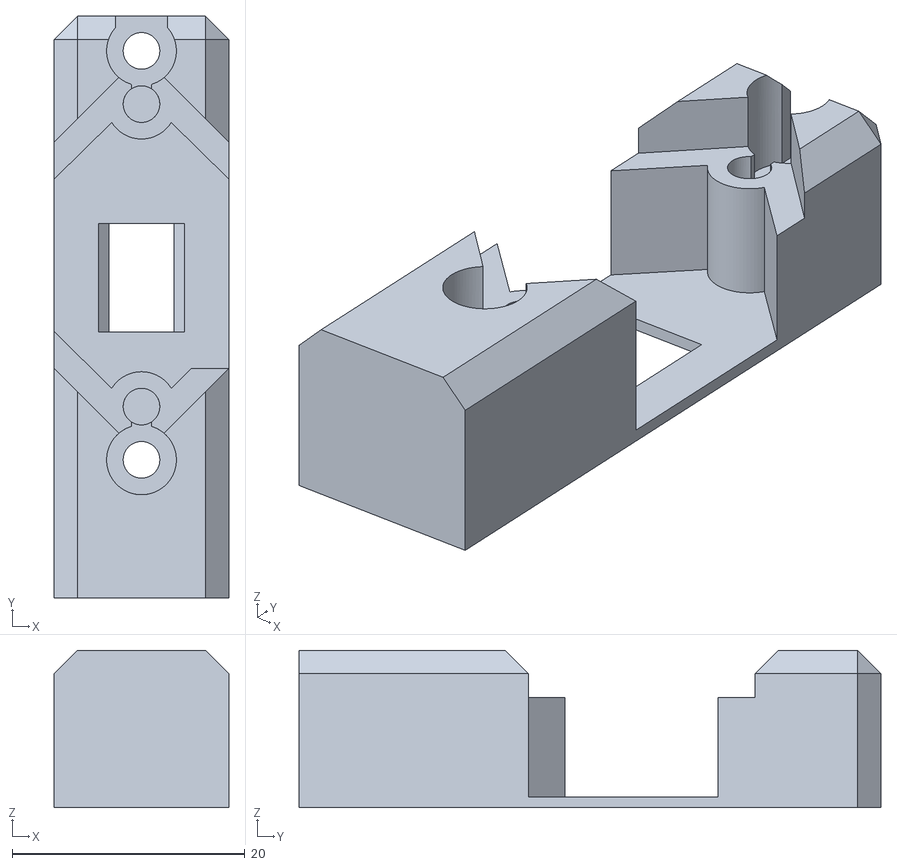
[picture p77: CAD file, 2023-04-13]
Usermods/richardjm/idle_idea/IdleIdea2 v13 - BlockA.stl
15.0 x 50.0 x 13.5
