richardjm/Crucible/Usermods/richardjm/idler_beefy/idler_b_housing.stl

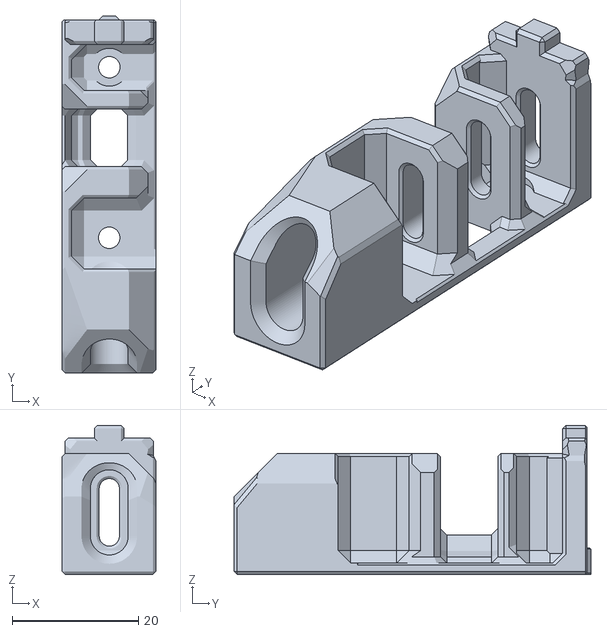
[picture p78: CAD file, 2023-03-04]
Usermods/richardjm/idler_beefy/idler_b_housing.stl
14.9 x 56.6 x 23.7
