richardjm/Crucible/Usermods/richardjm/puppet-pi-mount/Puppet.stl

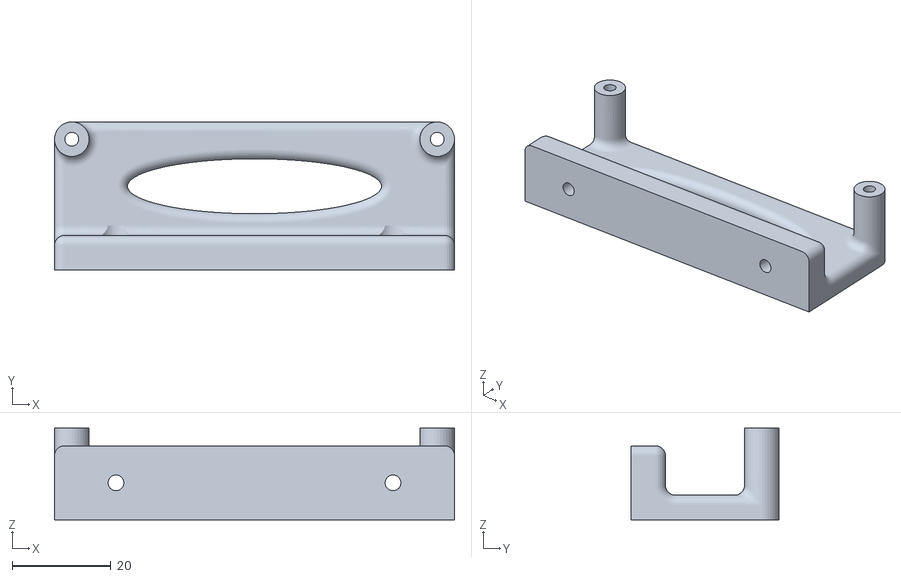
[picture p79: CAD file, 2023-03-19]
Usermods/richardjm/puppet-pi-mount/Puppet.stl
81.0 x 30.0 x 18.6
