richardjm/Crucible/Usermods/richardjm/short-rear-z/z_stepper_rear.stl

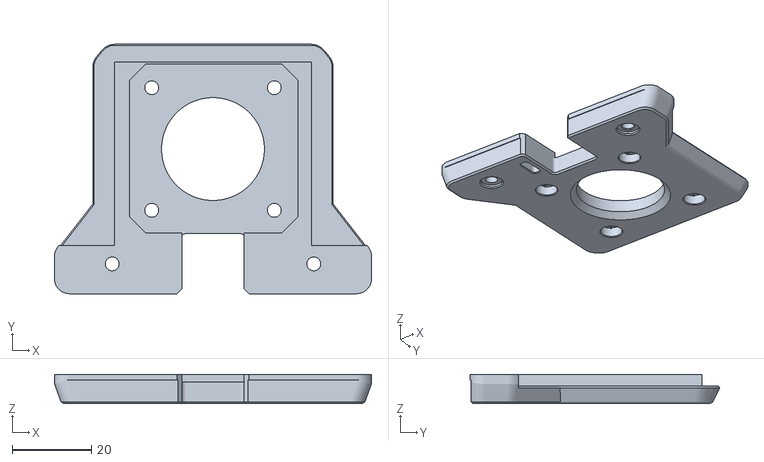
[picture p80: CAD file, 2023-02-24]
Usermods/richardjm/short-rear-z/z_stepper_rear.stl
80.2 x 63.1 x 7.45
