richardjm/Crucible/Usermods/richardjm/UnKlickyNG/STL/ProbeMount_Body1.stl

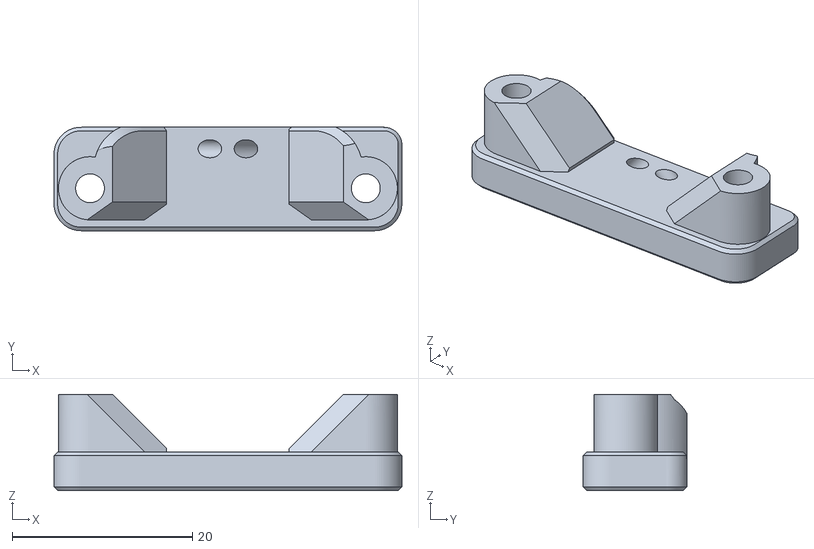
[picture p81: CAD file, 2023-03-06]
Usermods/richardjm/UnKlickyNG/STL/ProbeMount_Body1.stl
38.6 x 11.5 x 10.7
