richardjm/Crucible/STLs/display/[a]_Display_Faceplate_x1.stl

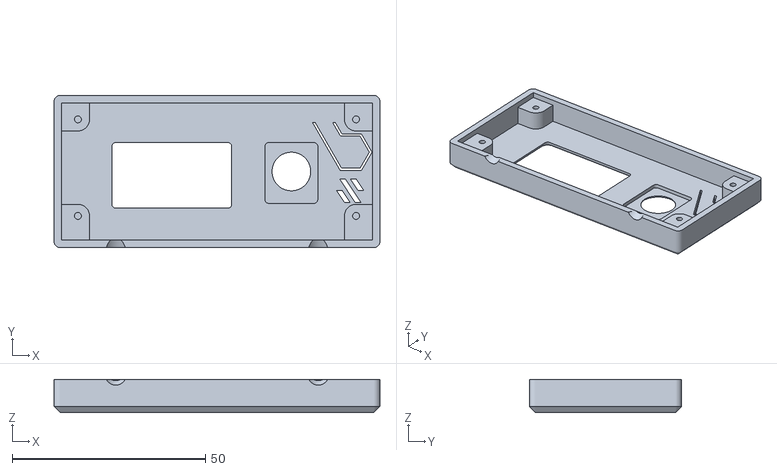
[picture p82: CAD file, 2023-03-23]
STLs/display/[a]_Display_Faceplate_x1.stl
84.4 x 39.4 x 8.63
