richardjm/Crucible/STLs/gantry/a_drive_upper_no_fittings.stl

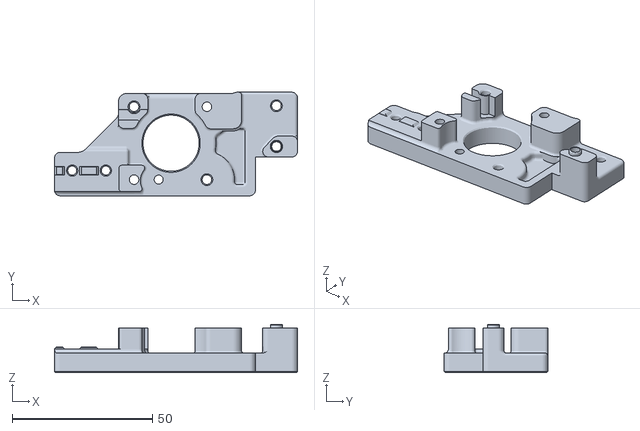
[picture p83: CAD file, 2023-02-11]
STLs/gantry/a_drive_upper_no_fittings.stl
86.7 x 36.9 x 17.3
