richardjm/Crucible/STLs/klicky/probe_dock.stl

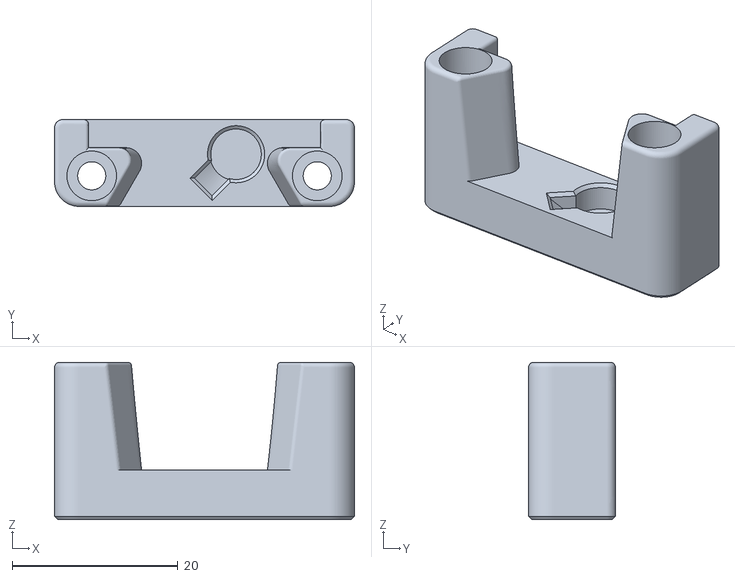
[picture p84: CAD file, 2023-02-26]
STLs/klicky/probe_dock.stl
36.3 x 10.5 x 19.0
