richardjm/Crucible/STLs/mini_stealthburner/[a]_strain_relief_spacers_x2.stl

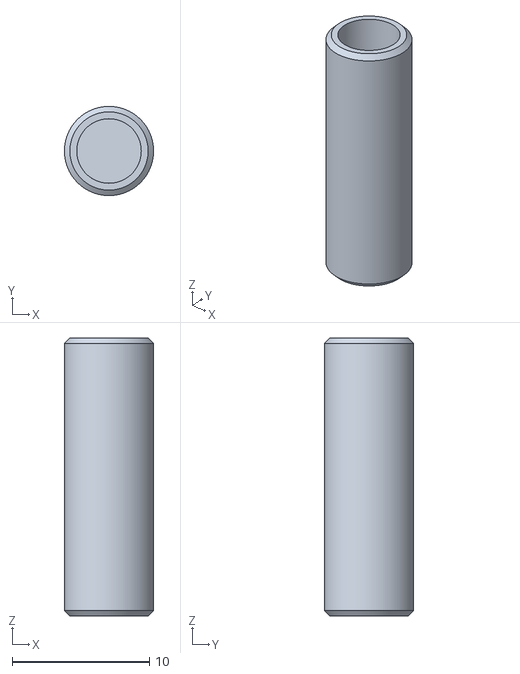
[picture p85: CAD file, 2023-02-12]
STLs/mini_stealthburner/[a]_strain_relief_spacers_x2.stl
6.50 x 6.50 x 20.2
