richardjm/Crucible/STLs/panels/door_hinge_x2.stl

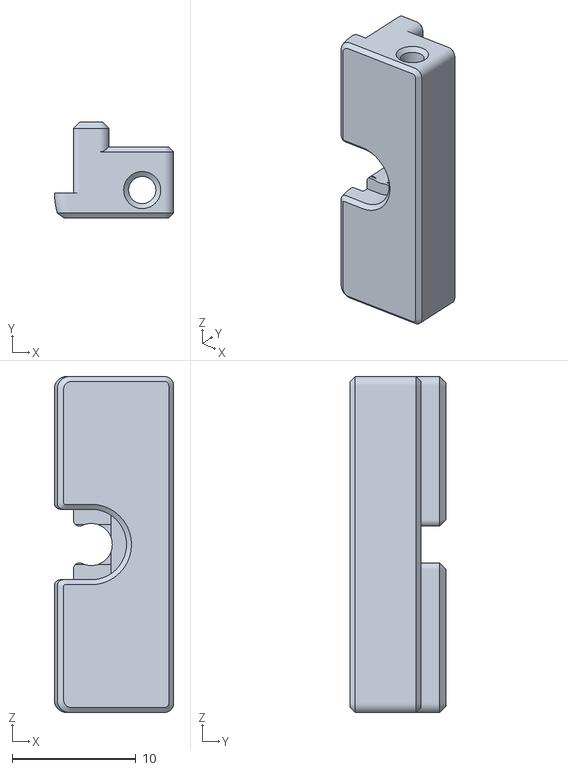
[picture p86: CAD file, 2023-01-31]
STLs/panels/door_hinge_x2.stl
9.67 x 7.75 x 27.2
