richardjm/Crucible/STLs/tools/1515DrillGuide2.stl

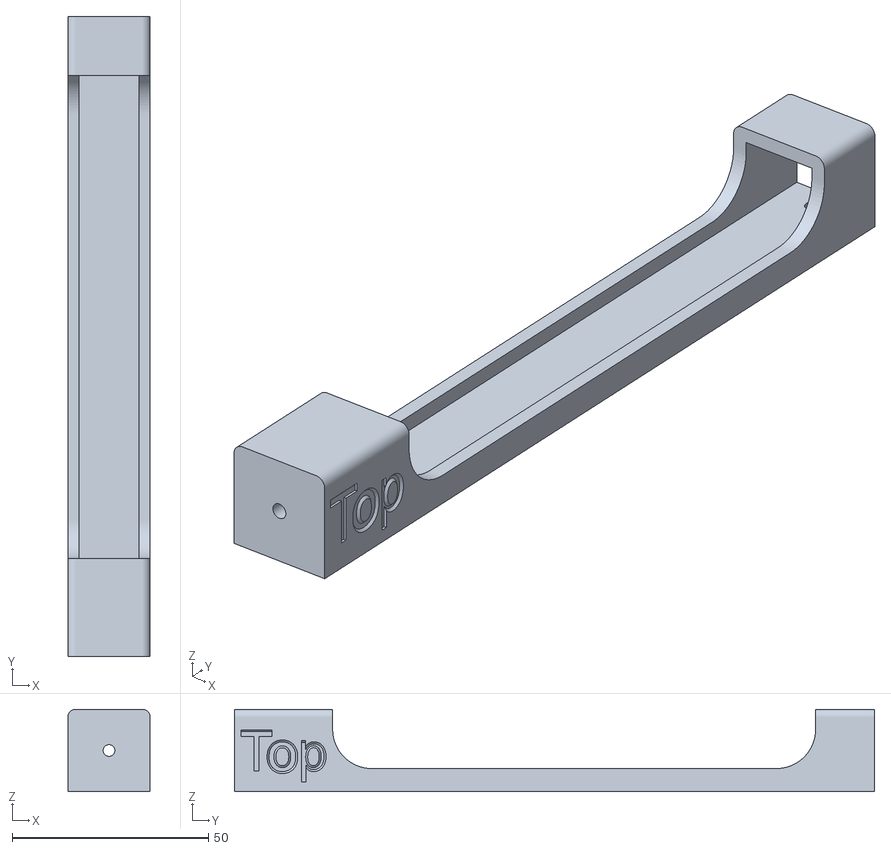
[picture p87: CAD file, 2023-02-13]
STLs/tools/1515DrillGuide2.stl
21.0 x 163.0 x 21.0
