richardjm/Crucible/STLs/z_assembly/z_bed_right_lower.stl

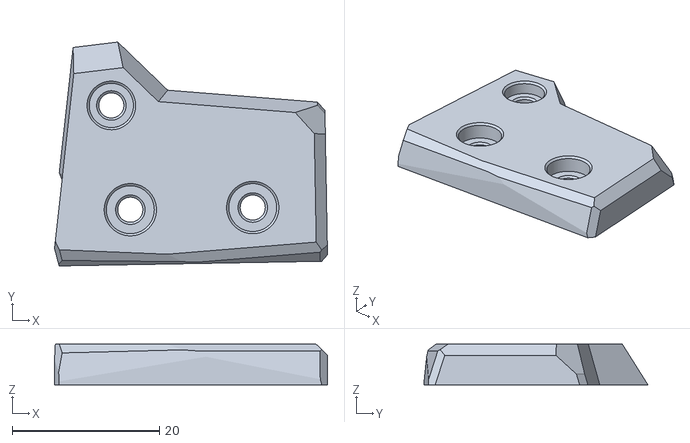
[picture p88: CAD file, 2023-02-03]
STLs/z_assembly/z_bed_right_lower.stl
37.1 x 30.4 x 5.50
