richardjm/Crucible/Usermods/richardjm/carriage-slimmed/[a]_x_carriage-4.stl

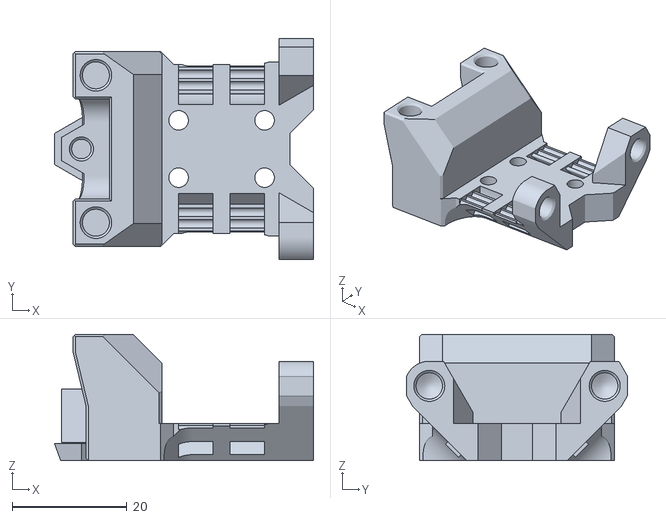
[picture p89: CAD file, 2023-02-16]
Usermods/richardjm/carriage-slimmed/[a]_x_carriage-4.stl
45.2 x 38.5 x 22.0
