richardjm/Crucible/Usermods/richardjm/everywhere-brace/z_left_upper_sliced.stl

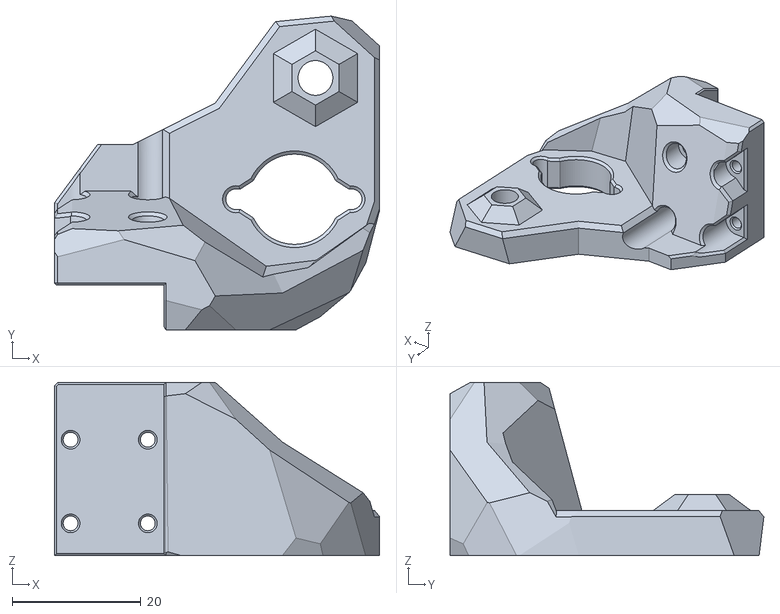
[picture p90: CAD file, 2023-11-12]
Usermods/richardjm/everywhere-brace/z_left_upper_sliced.stl
50.5 x 48.8 x 26.9
