richardjm/Crucible/Usermods/richardjm/extrusionless-x/boop/Boop_Upper_PCB v8.stl

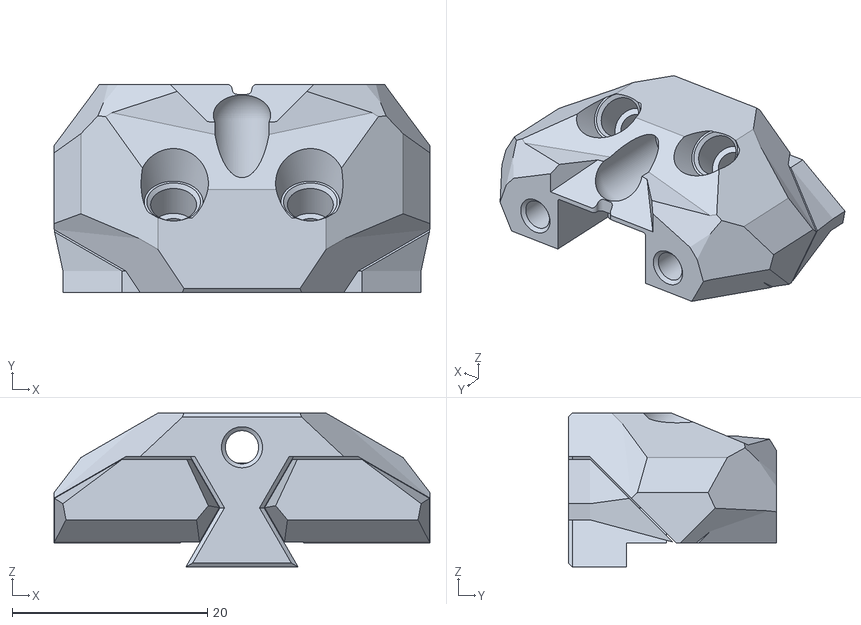
[picture p91: CAD file, 2025-10-05]
Usermods/richardjm/extrusionless-x/boop/Boop_Upper_PCB v8.stl
38.5 x 21.3 x 15.8
