richardjm/Crucible/Usermods/richardjm/extrusionless-x/XY_Joint_Left_Upper.stl

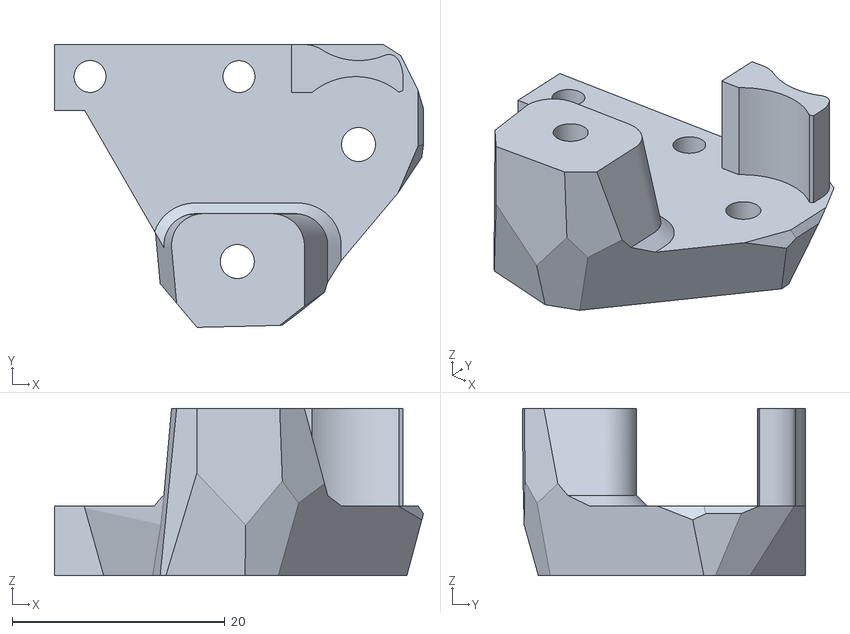
[picture p92: CAD file, 2025-10-05]
Usermods/richardjm/extrusionless-x/XY_Joint_Left_Upper.stl
34.7 x 26.6 x 15.7
