richardjm/Crucible/Usermods/richardjm/idle_idea/IdleIdea2 v13 - BlockB.stl

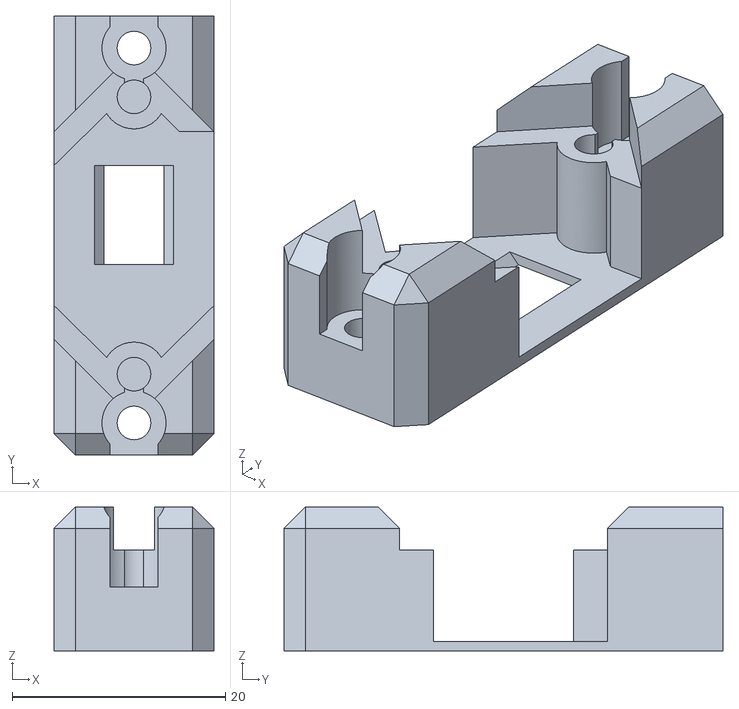
[picture p93: CAD file, 2023-04-13]
Usermods/richardjm/idle_idea/IdleIdea2 v13 - BlockB.stl
15.0 x 41.2 x 13.5
