richardjm/Crucible/Usermods/richardjm/UnKlickyNG/STL/ProbeMount_Body2.stl

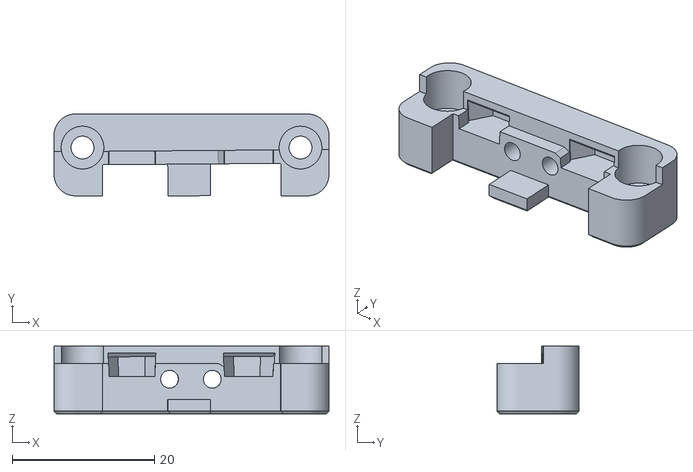
[picture p94: CAD file, 2023-03-06]
Usermods/richardjm/UnKlickyNG/STL/ProbeMount_Body2.stl
38.6 x 11.5 x 9.53
