richardjm/Crucible/STLs/display/Display_Knob_x1.stl

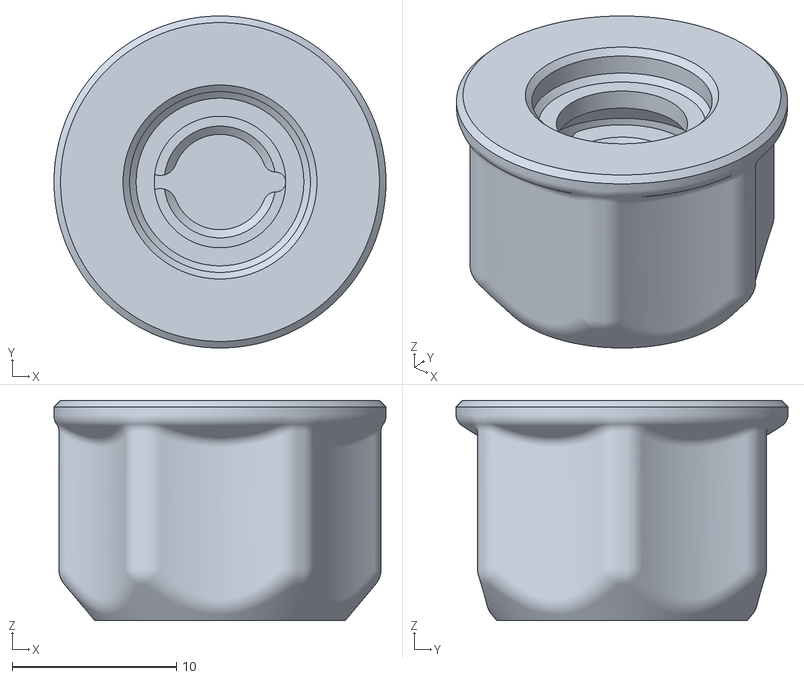
[picture p95: CAD file, 2023-03-23]
STLs/display/Display_Knob_x1.stl
20.2 x 20.2 x 13.4
