richardjm/Crucible/STLs/gantry/b_idler_adjuster_nologo.stl

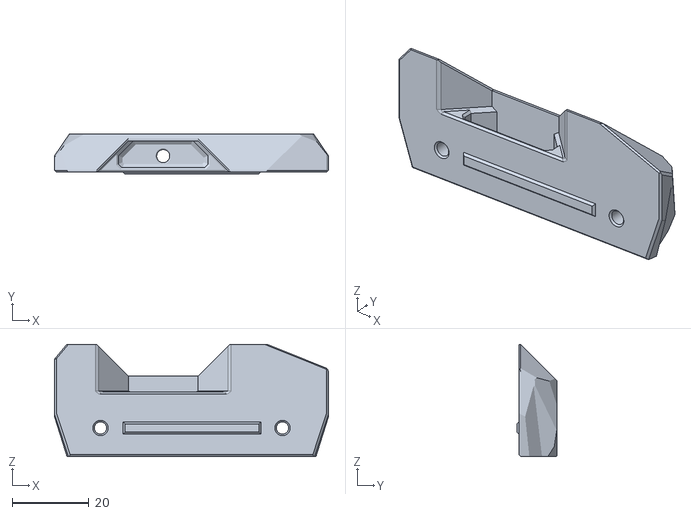
[picture p96: CAD file, 2023-01-31]
STLs/gantry/b_idler_adjuster_nologo.stl
71.5 x 10.5 x 29.3
