richardjm/Crucible/STLs/klicky/carriage_probe_mount_x1.stl

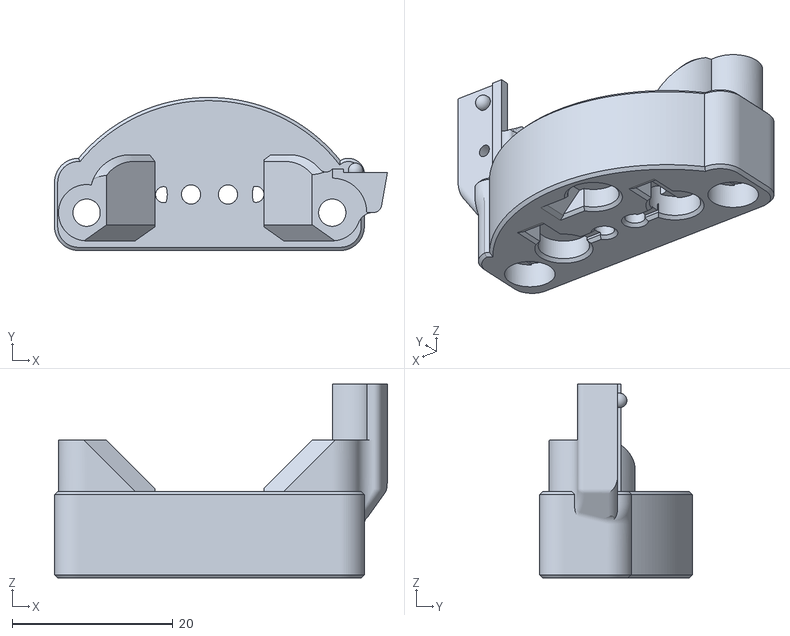
[picture p97: CAD file, 2023-02-12]
STLs/klicky/carriage_probe_mount_x1.stl
41.5 x 19.1 x 24.2
