richardjm/Crucible/STLs/mini_stealthburner/[a]_extruder_midbody.stl

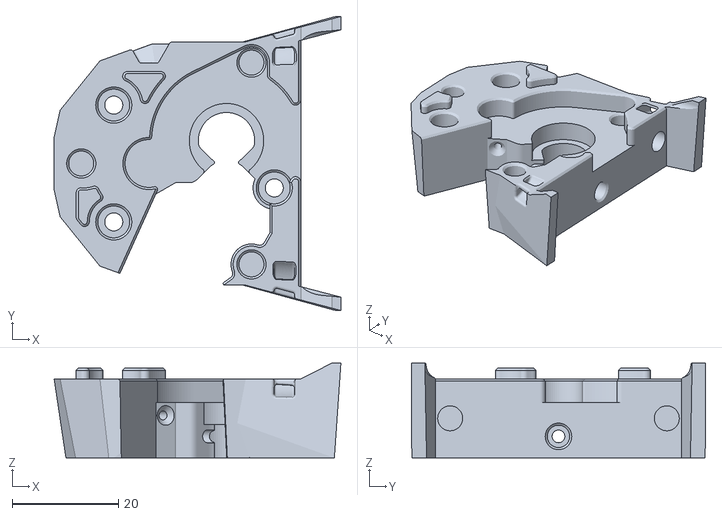
[picture p98: CAD file, 2023-02-12]
STLs/mini_stealthburner/[a]_extruder_midbody.stl
54.0 x 55.4 x 17.8
