richardjm/Crucible/STLs/panels/door_latch_magnets_x2.stl

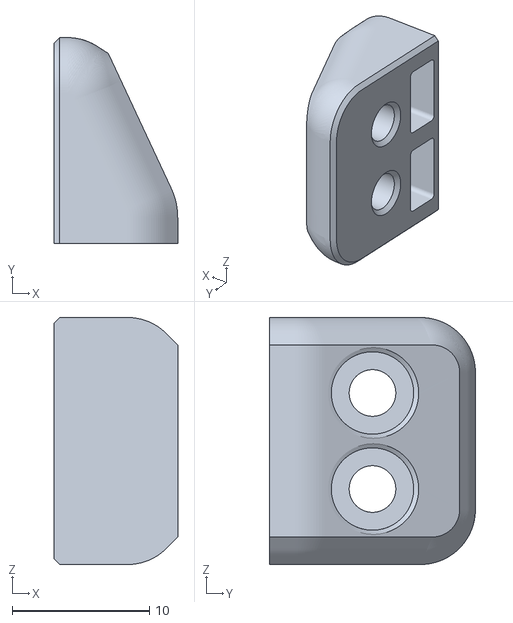
[picture p99: CAD file, 2023-01-31]
STLs/panels/door_latch_magnets_x2.stl
9.00 x 15.0 x 18.0
