richardjm/Crucible/STLs/stealth_skirts/Foot_Accent_B_x2.stl

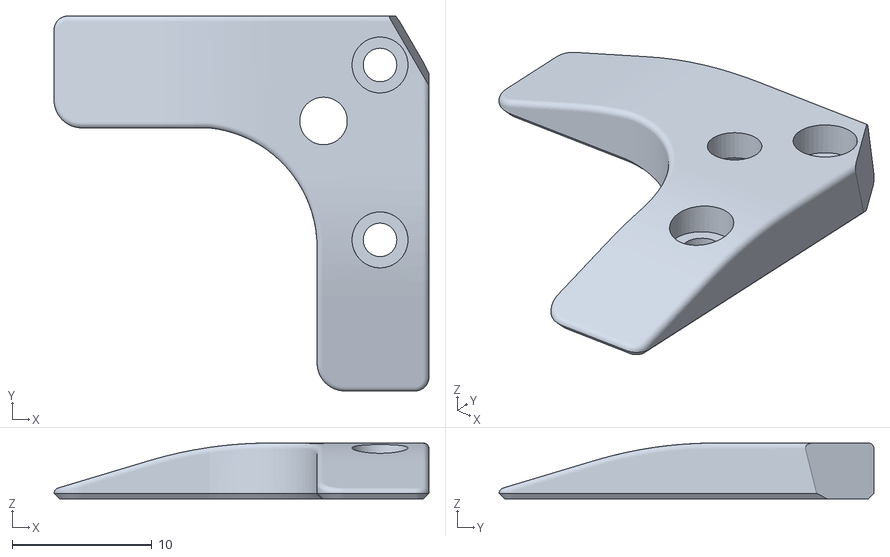
[picture p100: CAD file, 2023-03-23]
STLs/stealth_skirts/Foot_Accent_B_x2.stl
26.8 x 26.8 x 4.00
