richardjm/Crucible/STLs/tools/1515DrillGuide.stl

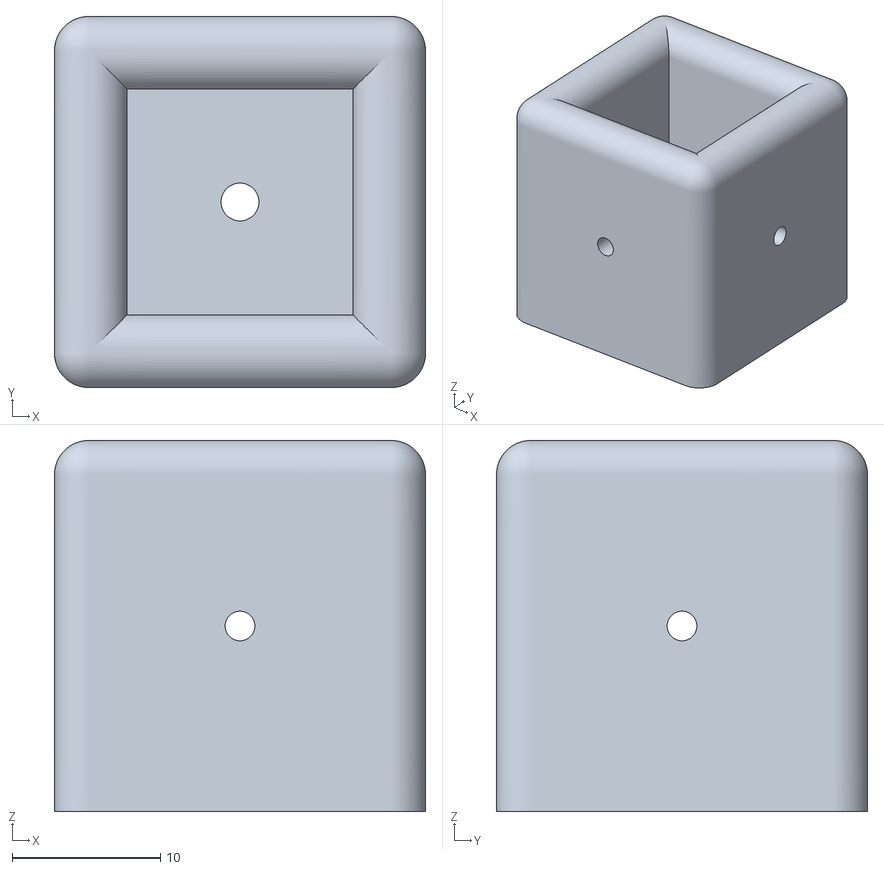
[picture p101: CAD file, 2023-02-12]
STLs/tools/1515DrillGuide.stl
25.0 x 25.0 x 25.0
