richardjm/Crucible/STLs/z_assembly/z_bed_right_upper.stl

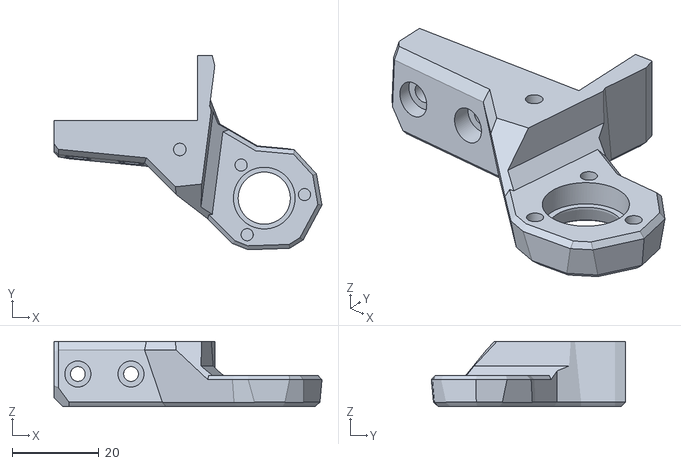
[picture p102: CAD file, 2023-02-03]
STLs/z_assembly/z_bed_right_upper.stl
61.7 x 44.8 x 15.0
