richardjm/Crucible/Usermods/richardjm/everywhere-brace/CrucibleBrace_Base_Left_Short.stl

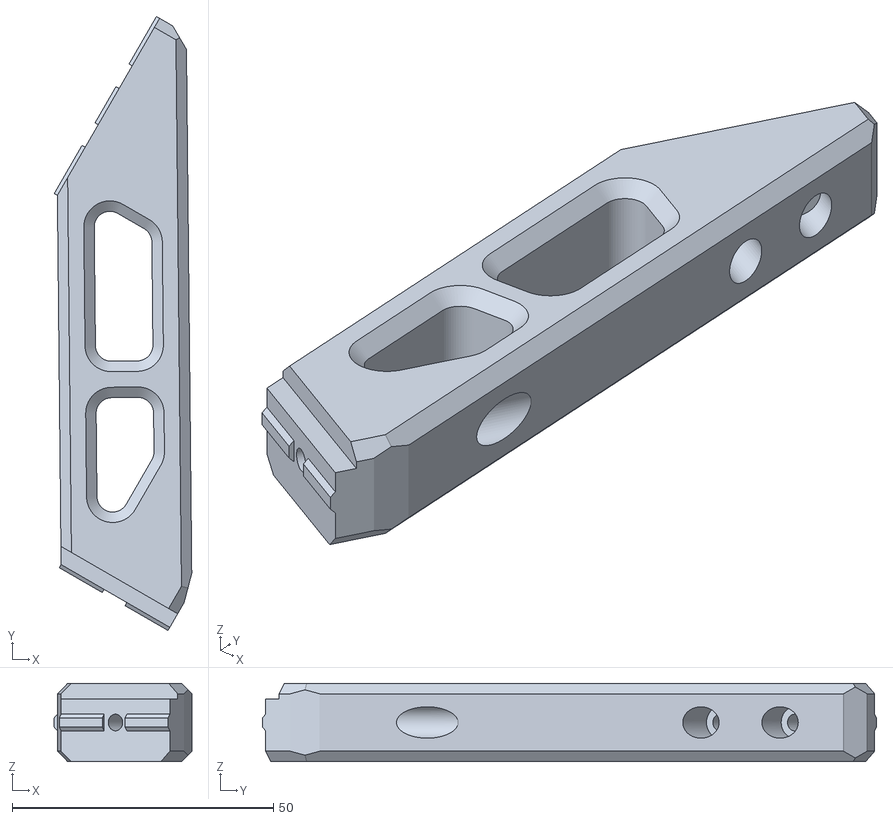
[picture p103: CAD file, 2023-02-14]
Usermods/richardjm/everywhere-brace/CrucibleBrace_Base_Left_Short.stl
26.3 x 117.6 x 15.0
