richardjm/Crucible/Usermods/richardjm/extrusionless-x/boop/[a]_boop_center_optical (1).stl

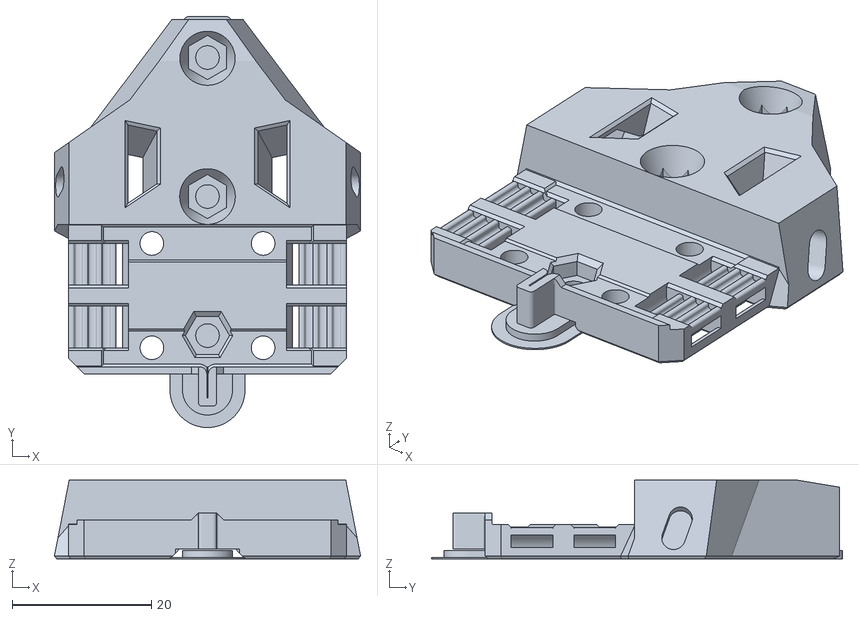
[picture p104: CAD file, 2025-10-05]
Usermods/richardjm/extrusionless-x/boop/[a]_boop_center_optical (1).stl
44.0 x 59.1 x 11.3
