richardjm/Crucible/Usermods/richardjm/extrusionless-x/XY_Joint_Left_Lower.stl

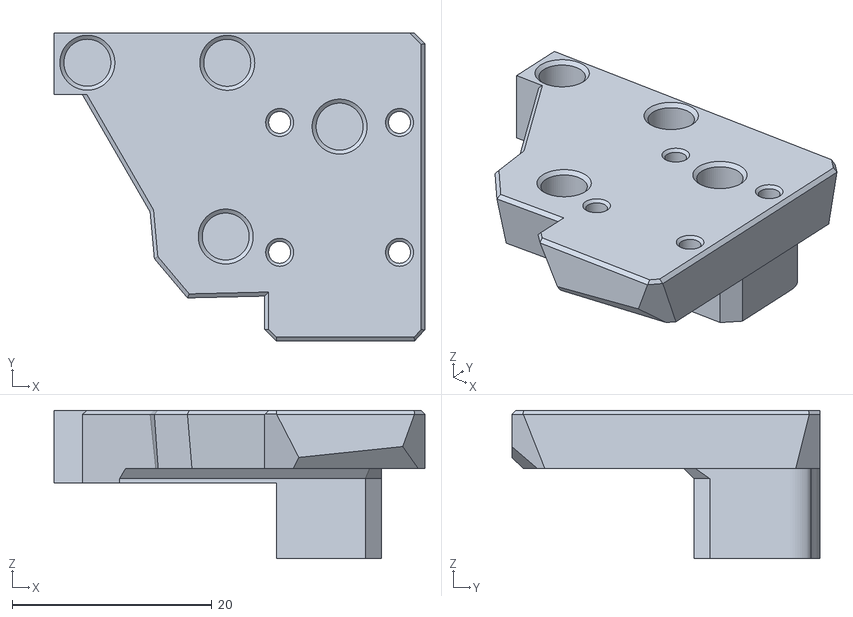
[picture p105: CAD file, 2025-10-05]
Usermods/richardjm/extrusionless-x/XY_Joint_Left_Lower.stl
37.1 x 30.9 x 14.8
