richardjm/Crucible/Usermods/richardjm/idle_idea/IdleIdea2 v11 - RailStop.stl

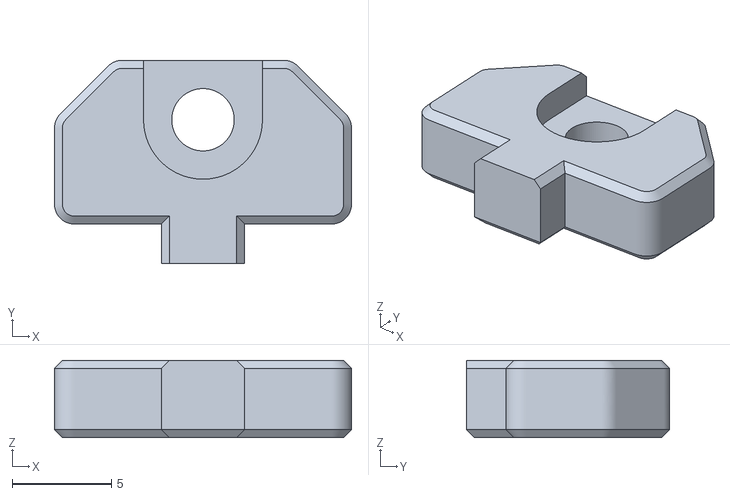
[picture p106: CAD file, 2023-04-13]
Usermods/richardjm/idle_idea/IdleIdea2 v11 - RailStop.stl
15.0 x 10.3 x 3.90
