richardjm/Crucible/Usermods/richardjm/UnKlickyNG/STL/ProbeMount_Body3.stl

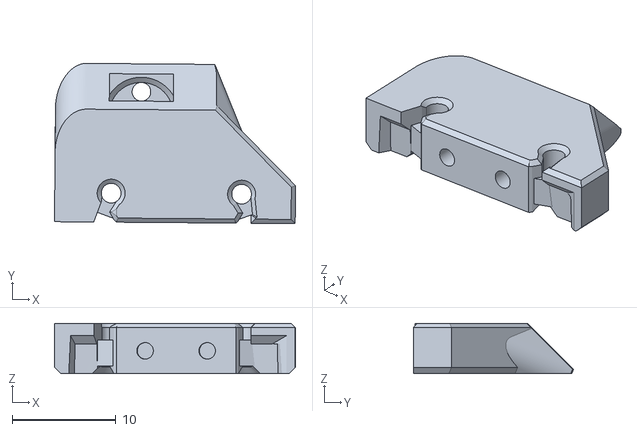
[picture p107: CAD file, 2023-03-06]
Usermods/richardjm/UnKlickyNG/STL/ProbeMount_Body3.stl
23.3 x 15.5 x 4.85
