richardjm/Crucible/STLs/frame/rear_vertical_brace.stl

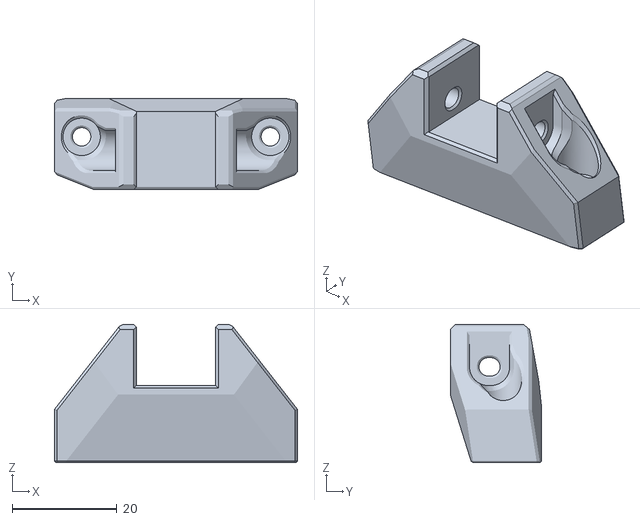
[picture p108: CAD file, 2023-01-31]
STLs/frame/rear_vertical_brace.stl
46.5 x 17.5 x 26.4
