richardjm/Crucible/STLs/klicky/carriage_probe_mount_no_fitting_x1.stl

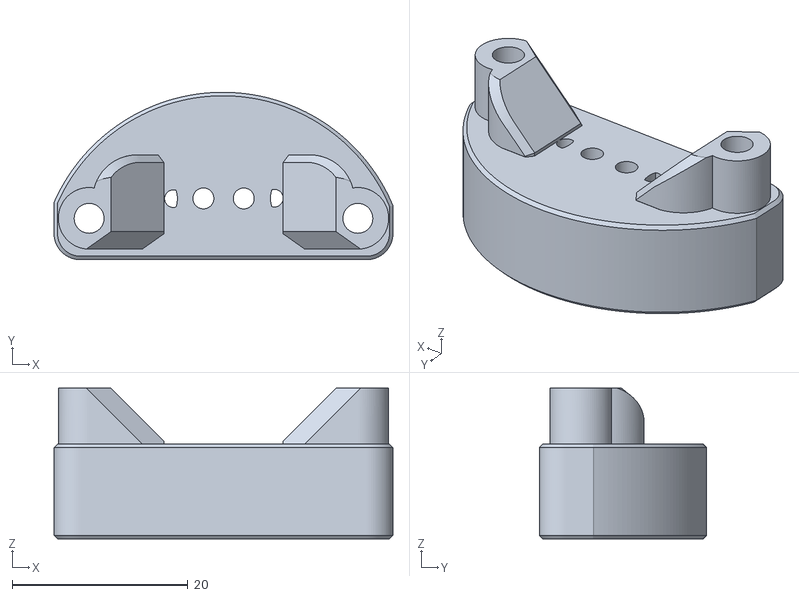
[picture p109: CAD file, 2023-02-12]
STLs/klicky/carriage_probe_mount_no_fitting_x1.stl
38.6 x 19.1 x 17.2
