richardjm/Crucible/STLs/mini_stealthburner/[t]_shuttle.stl

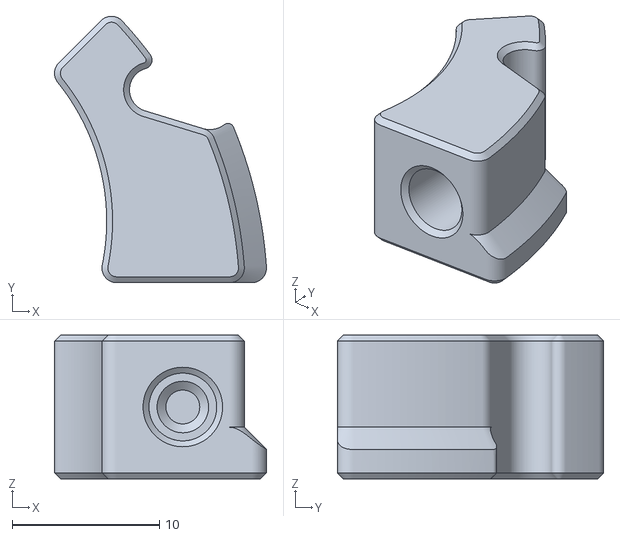
[picture p110: CAD file, 2023-02-12]
STLs/mini_stealthburner/[t]_shuttle.stl
14.4 x 18.1 x 9.75
