richardjm/Crucible/STLs/panels/door_latch_bottom.stl

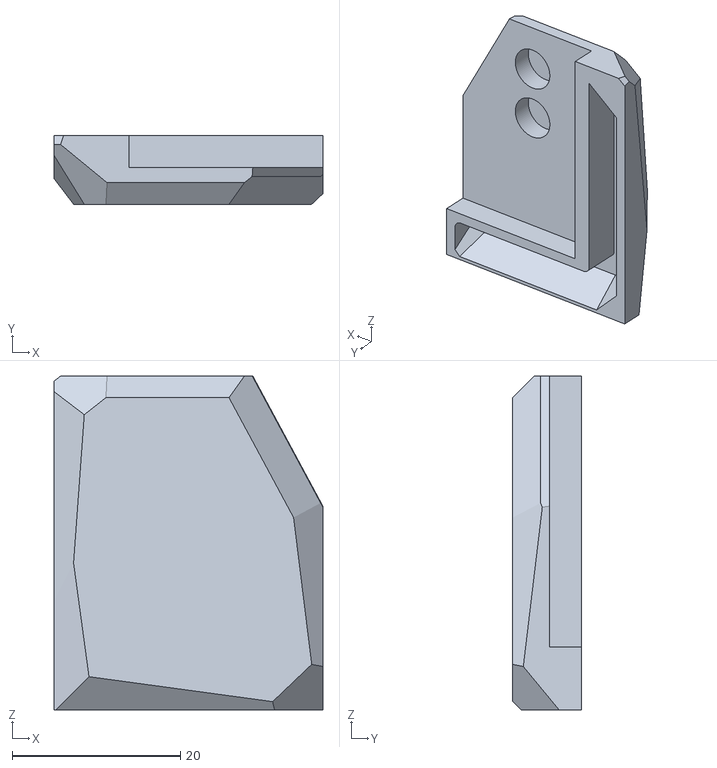
[picture p111: CAD file, 2023-01-31]
STLs/panels/door_latch_bottom.stl
32.0 x 8.16 x 39.8
