richardjm/Crucible/STLs/z_assembly/z_stepper_left.stl

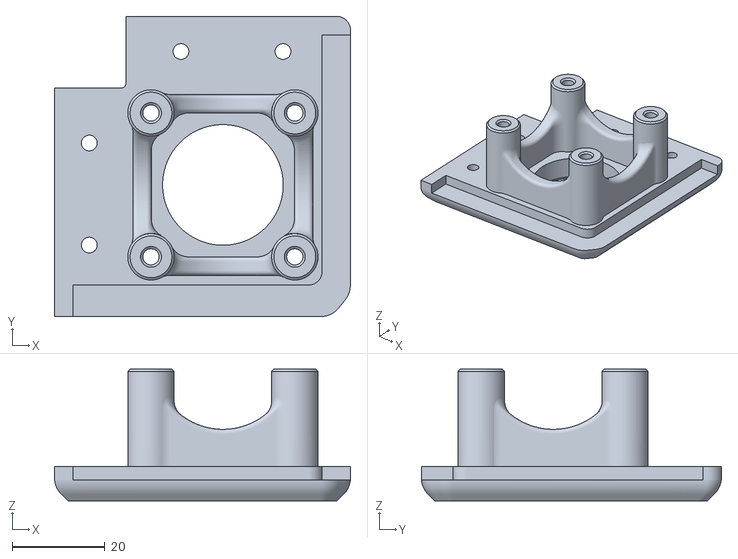
[picture p112: CAD file, 2023-01-31]
STLs/z_assembly/z_stepper_left.stl
63.8 x 64.7 x 28.4
