richardjm/Crucible/Usermods/richardjm/extrusionless-x/XY_Joint_Right_Upper.stl

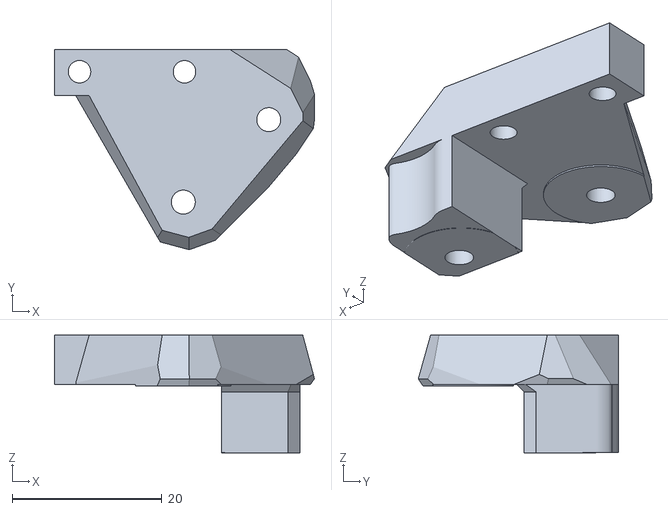
[picture p113: CAD file, 2025-10-05]
Usermods/richardjm/extrusionless-x/XY_Joint_Right_Upper.stl
34.7 x 26.8 x 15.7
