richardjm/Crucible/Usermods/richardjm/UnKlickyNG/STL/KlickyNG_BFP_Unklicky_WhistlinRic_Front_2p6mm.stl

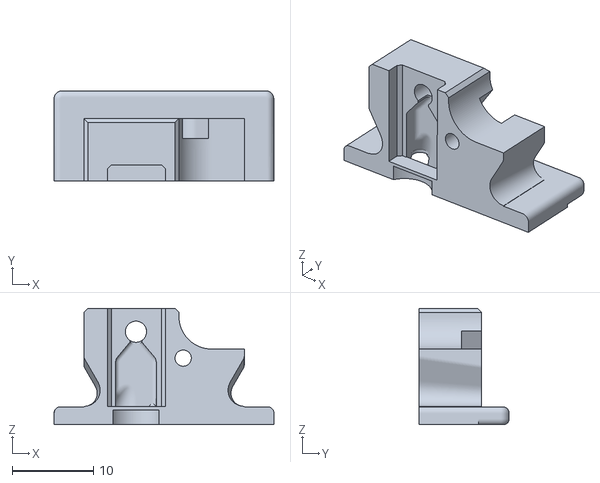
[picture p114: CAD file, 2023-03-06]
Usermods/richardjm/UnKlickyNG/STL/KlickyNG_BFP_Unklicky_WhistlinRic_Front_2p6mm.stl
27.1 x 11.1 x 14.3
