richardjm/Crucible/STLs/mini_stealthburner/[a]_x_carriage.stl

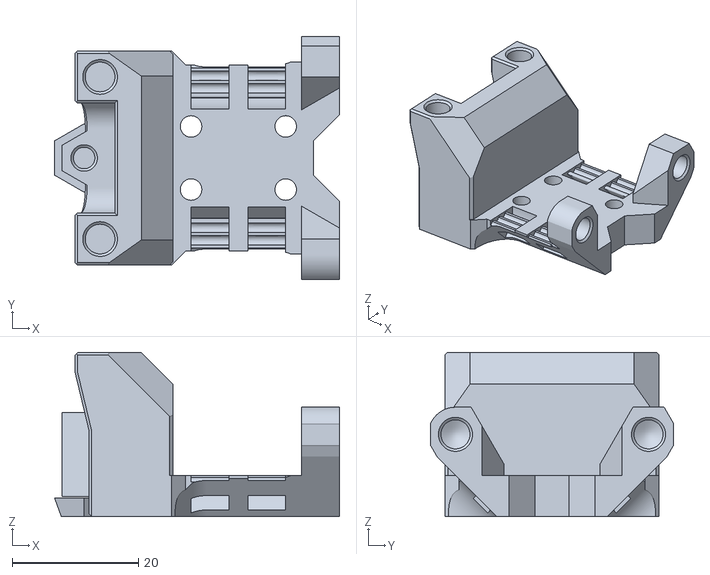
[picture p115: CAD file, 2023-02-12]
STLs/mini_stealthburner/[a]_x_carriage.stl
45.2 x 38.5 x 26.0
