richardjm/Crucible/STLs/panels/door_latch_top.stl

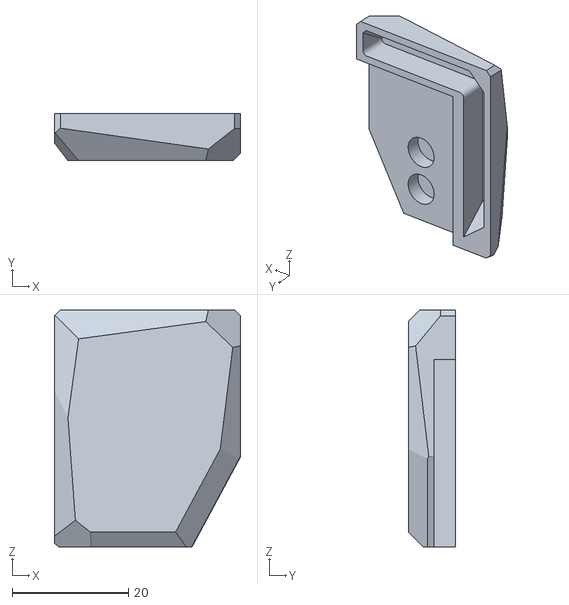
[picture p116: CAD file, 2023-01-31]
STLs/panels/door_latch_top.stl
32.0 x 8.16 x 40.8
