richardjm/Crucible/STLs/stealth_skirts/4010_Fan_Grill_x2.stl

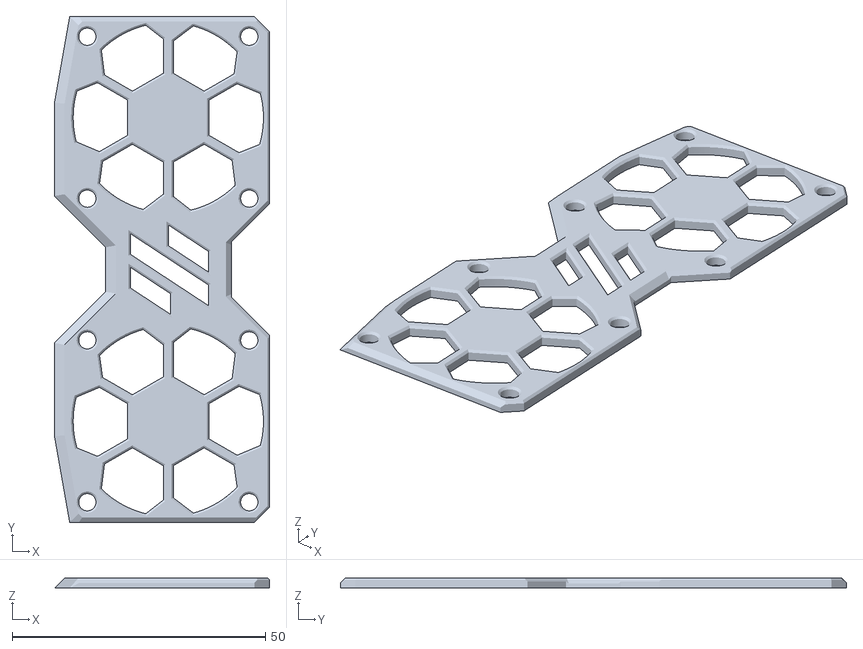
[picture p117: CAD file, 2023-03-23]
STLs/stealth_skirts/4010_Fan_Grill_x2.stl
42.5 x 100.0 x 2.00
