richardjm/Crucible/STLs/z_assembly/undercarriage_fan.stl

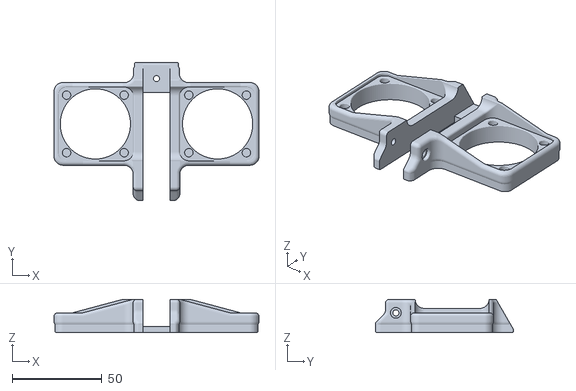
[picture p118: CAD file, 2023-01-31]
STLs/z_assembly/undercarriage_fan.stl
114.0 x 76.8 x 18.5
