richardjm/Crucible/Usermods/richardjm/UnKlickyNG/STL/ProbeMount_Body2_3mm.stl

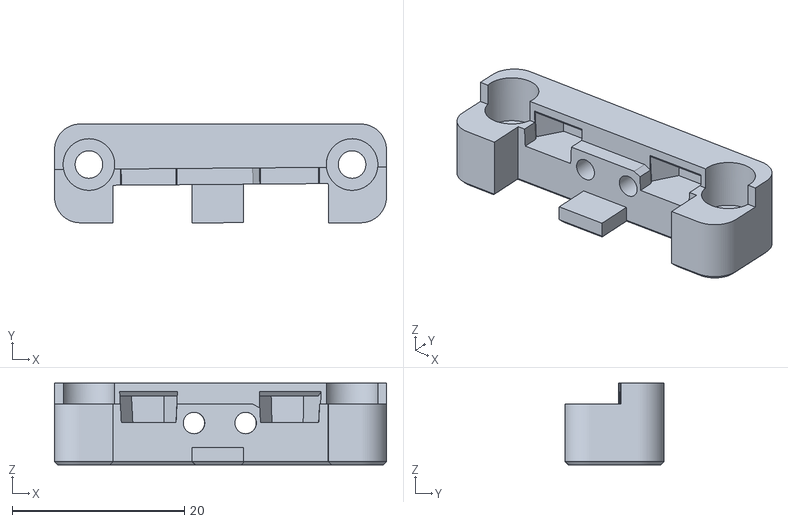
[picture p119: CAD file, 2023-03-06]
Usermods/richardjm/UnKlickyNG/STL/ProbeMount_Body2_3mm.stl
38.6 x 11.5 x 9.53
