richardjm/Crucible/STLs/gantry/xy_joint_left_upper.stl

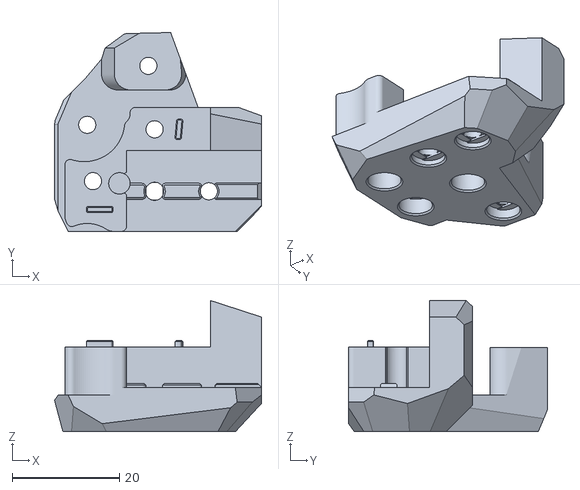
[picture p120: CAD file, 2023-01-31]
STLs/gantry/xy_joint_left_upper.stl
38.6 x 37.1 x 24.5
