richardjm/Crucible/STLs/mini_stealthburner/[t]_latch.stl

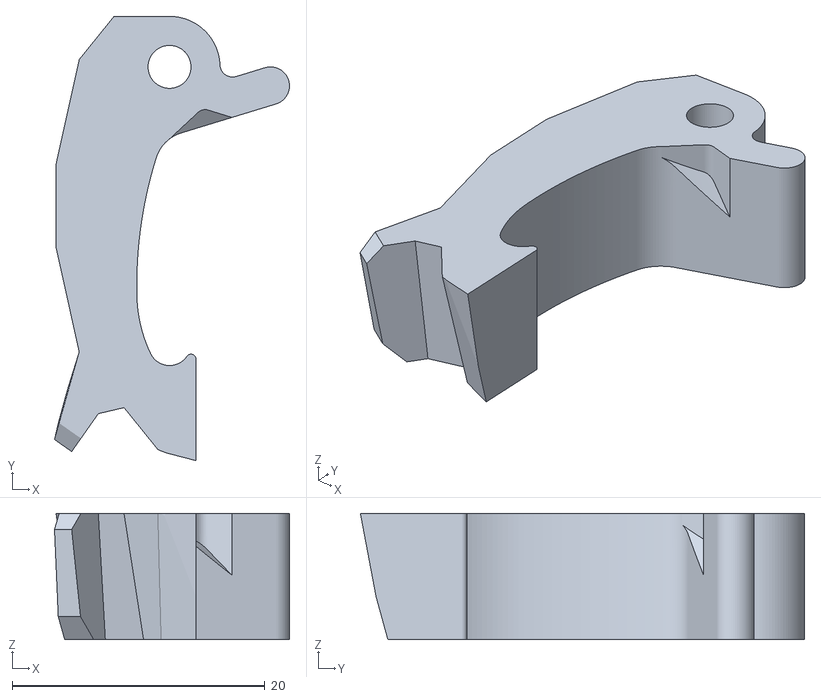
[picture p121: CAD file, 2023-02-12]
STLs/mini_stealthburner/[t]_latch.stl
18.6 x 35.2 x 10.0
