richardjm/Crucible/STLs/panels/[t]_handle_front.stl

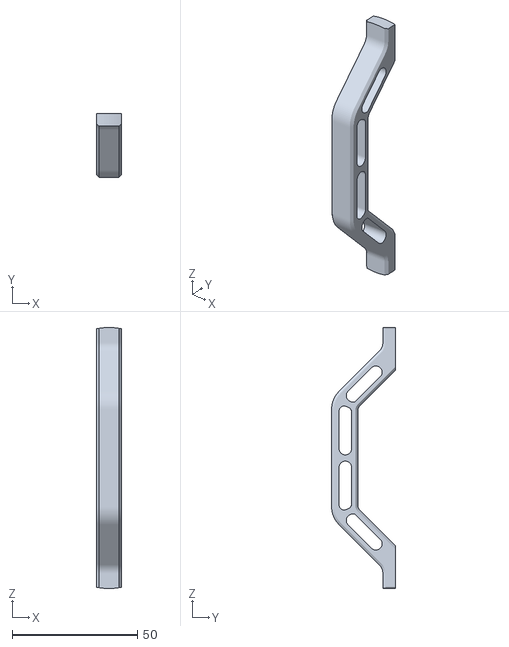
[picture p122: CAD file, 2023-01-31]
STLs/panels/[t]_handle_front.stl
10.0 x 25.5 x 104.3
