richardjm/Crucible/STLs/stealth_skirts/Right_Front_Foot_x1.stl

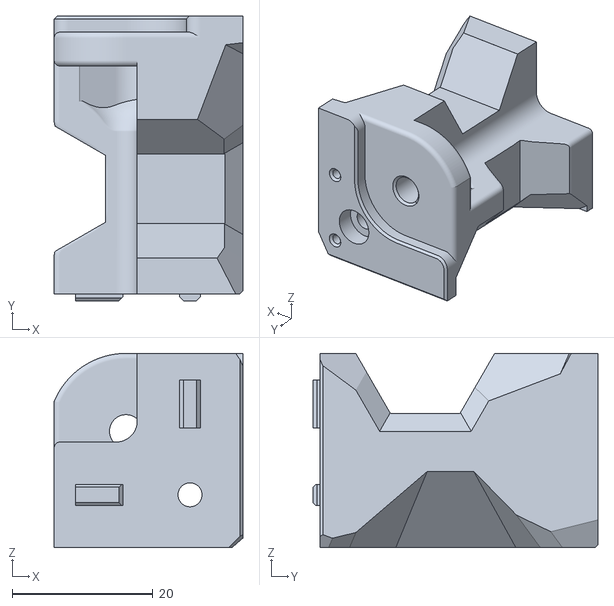
[picture p123: CAD file, 2023-03-23]
STLs/stealth_skirts/Right_Front_Foot_x1.stl
26.8 x 40.5 x 27.6
