richardjm/Crucible/STLs/z_assembly/[a]_z_rear_lower.stl

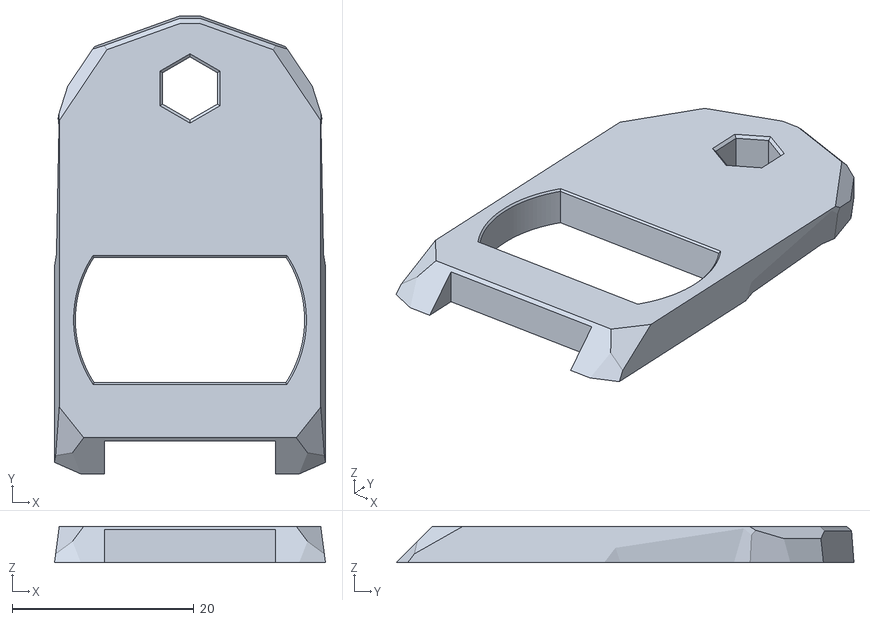
[picture p124: CAD file, 2023-01-31]
STLs/z_assembly/[a]_z_rear_lower.stl
29.8 x 50.4 x 4.00
