richardjm/Crucible/Usermods/richardjm/UnKlickyNG/STL/KlickyNG_BFP_Unklicky_Pin_3mm.stl

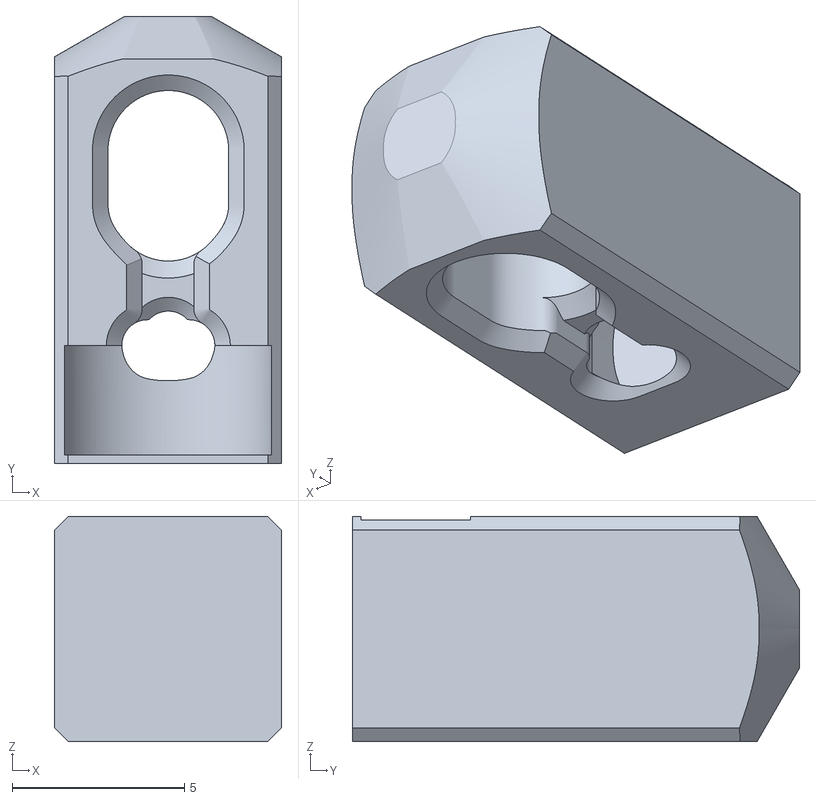
[picture p125: CAD file, 2023-03-06]
Usermods/richardjm/UnKlickyNG/STL/KlickyNG_BFP_Unklicky_Pin_3mm.stl
6.60 x 13.0 x 6.54
