richardjm/Crucible/STLs/gantry/[a]_b_idler_pulley.stl

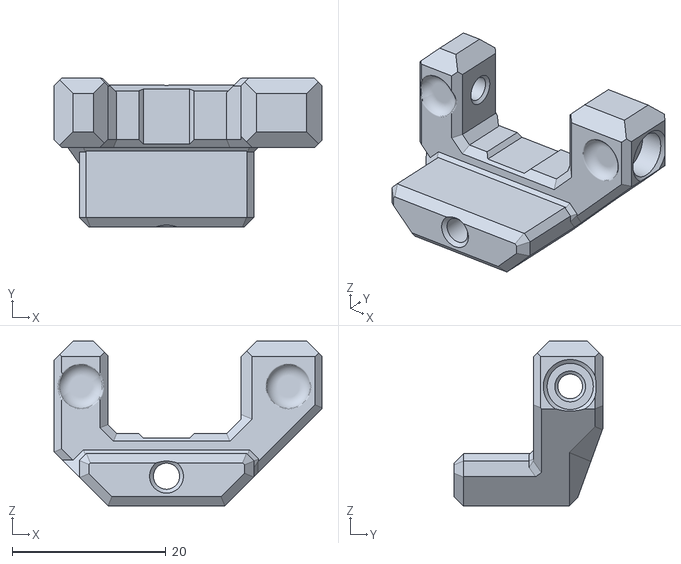
[picture p126: CAD file, 2023-01-31]
STLs/gantry/[a]_b_idler_pulley.stl
34.9 x 19.4 x 21.4
