richardjm/Crucible/STLs/panels/door_hinge_plate_x2.stl

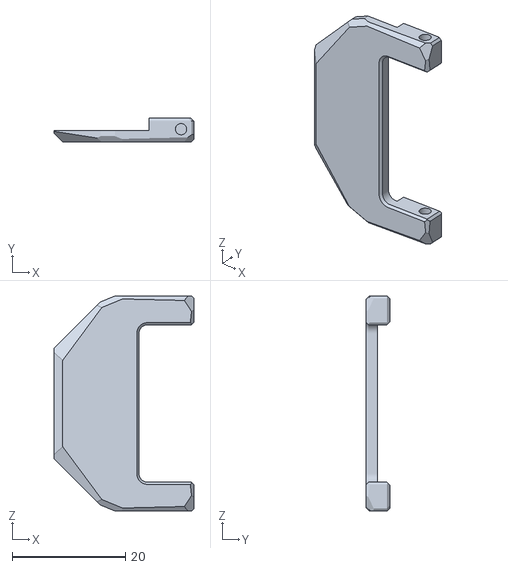
[picture p127: CAD file, 2023-01-31]
STLs/panels/door_hinge_plate_x2.stl
24.7 x 4.20 x 38.0
