richardjm/Crucible/STLs/stealth_skirts/Side_Logo_Insert_x2.stl

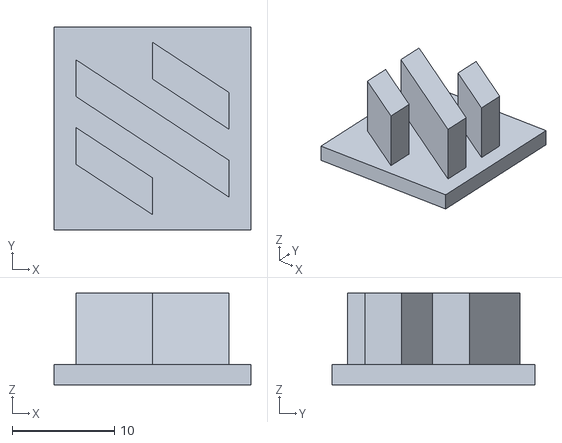
[picture p128: CAD file, 2023-03-23]
STLs/stealth_skirts/Side_Logo_Insert_x2.stl
19.3 x 19.9 x 9.00
