richardjm/Crucible/Usermods/richardjm/UnKlickyNG/STL/KlickyNG_Probe_Dock.stl

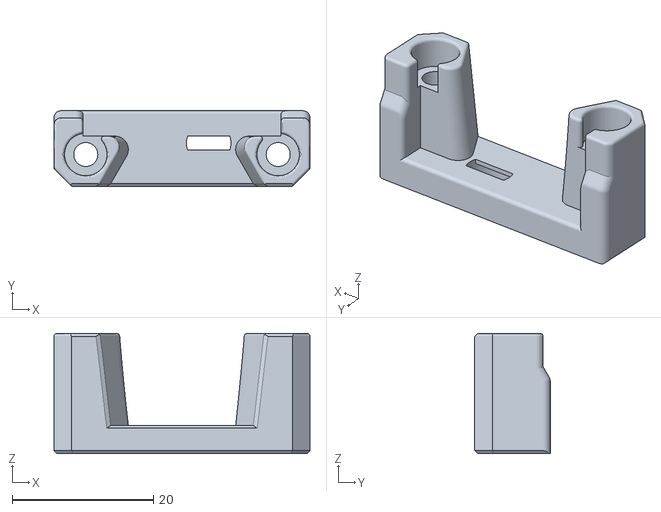
[picture p129: CAD file, 2023-03-06]
Usermods/richardjm/UnKlickyNG/STL/KlickyNG_Probe_Dock.stl
36.3 x 10.7 x 17.0
