richardjm/Crucible/STLs/gantry/y_endstop_trigger.stl

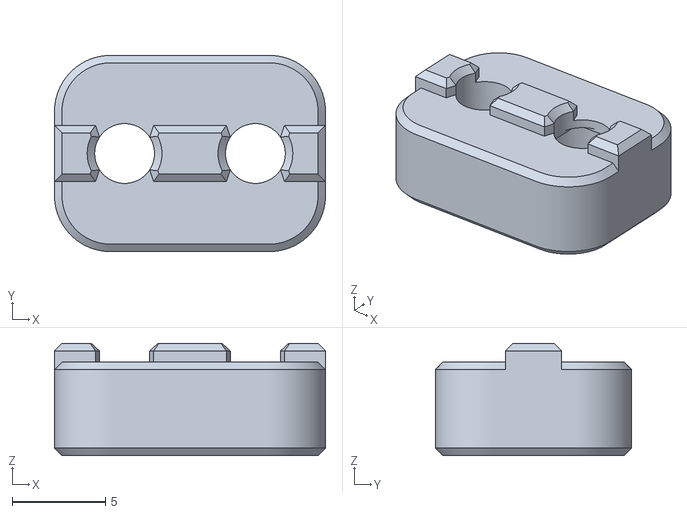
[picture p130: CAD file, 2023-01-31]
STLs/gantry/y_endstop_trigger.stl
14.5 x 10.5 x 6.00
