richardjm/Crucible/STLs/stealth_skirts/3510_Side_Skirt_Mid_x2.stl

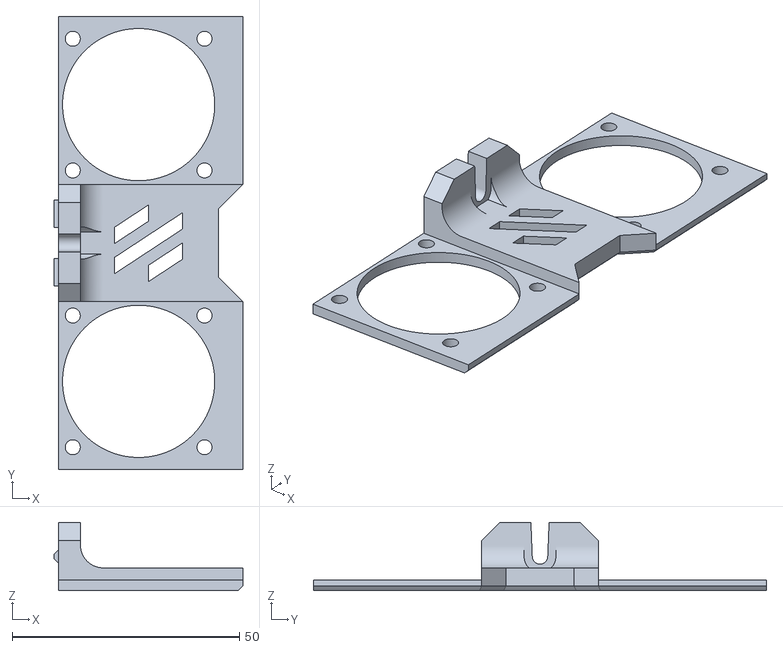
[picture p131: CAD file, 2023-03-23]
STLs/stealth_skirts/3510_Side_Skirt_Mid_x2.stl
41.5 x 99.7 x 15.0
