richardjm/Crucible/STLs/z_assembly/[a]_z_left_lower.stl

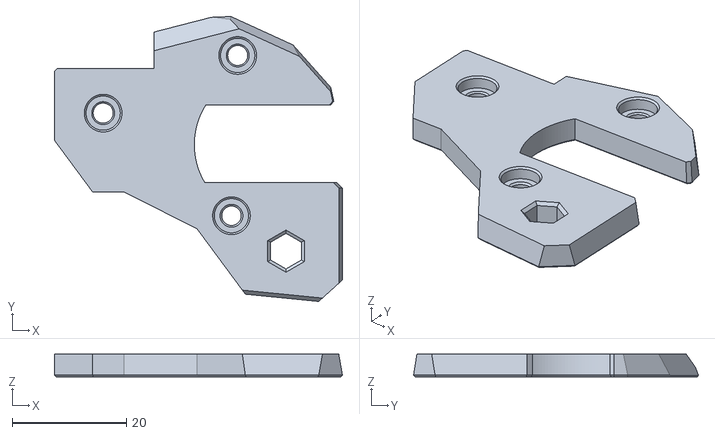
[picture p132: CAD file, 2023-01-31]
STLs/z_assembly/[a]_z_left_lower.stl
50.4 x 49.9 x 4.00
