richardjm/Crucible/STLs/gantry/[a]_a_idler_pulley.stl

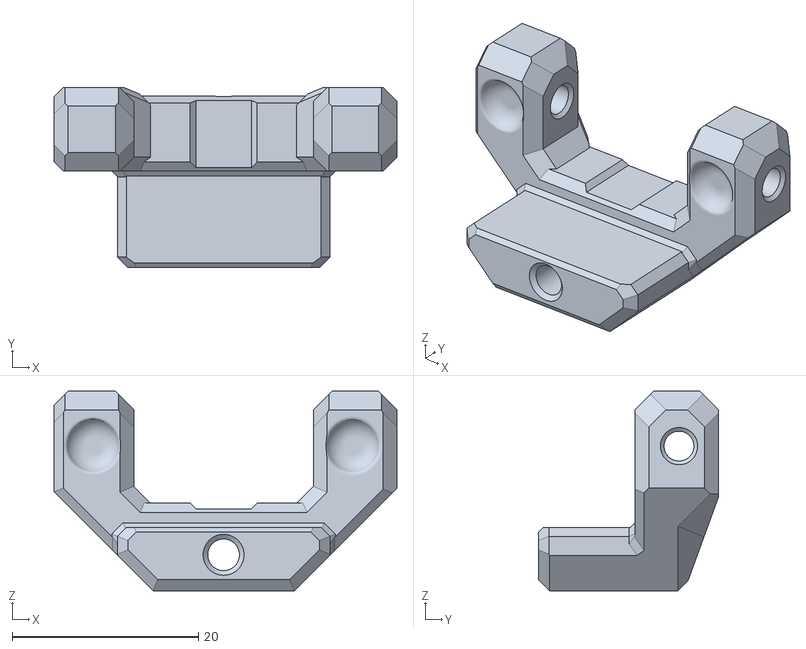
[picture p133: CAD file, 2023-01-31]
STLs/gantry/[a]_a_idler_pulley.stl
36.9 x 19.4 x 21.4
